RGBeter/Neptune/32X_main1.kicad_sch

## KiCad design 32X_main1.kicad_sch (2025-06-25, an earlier design)

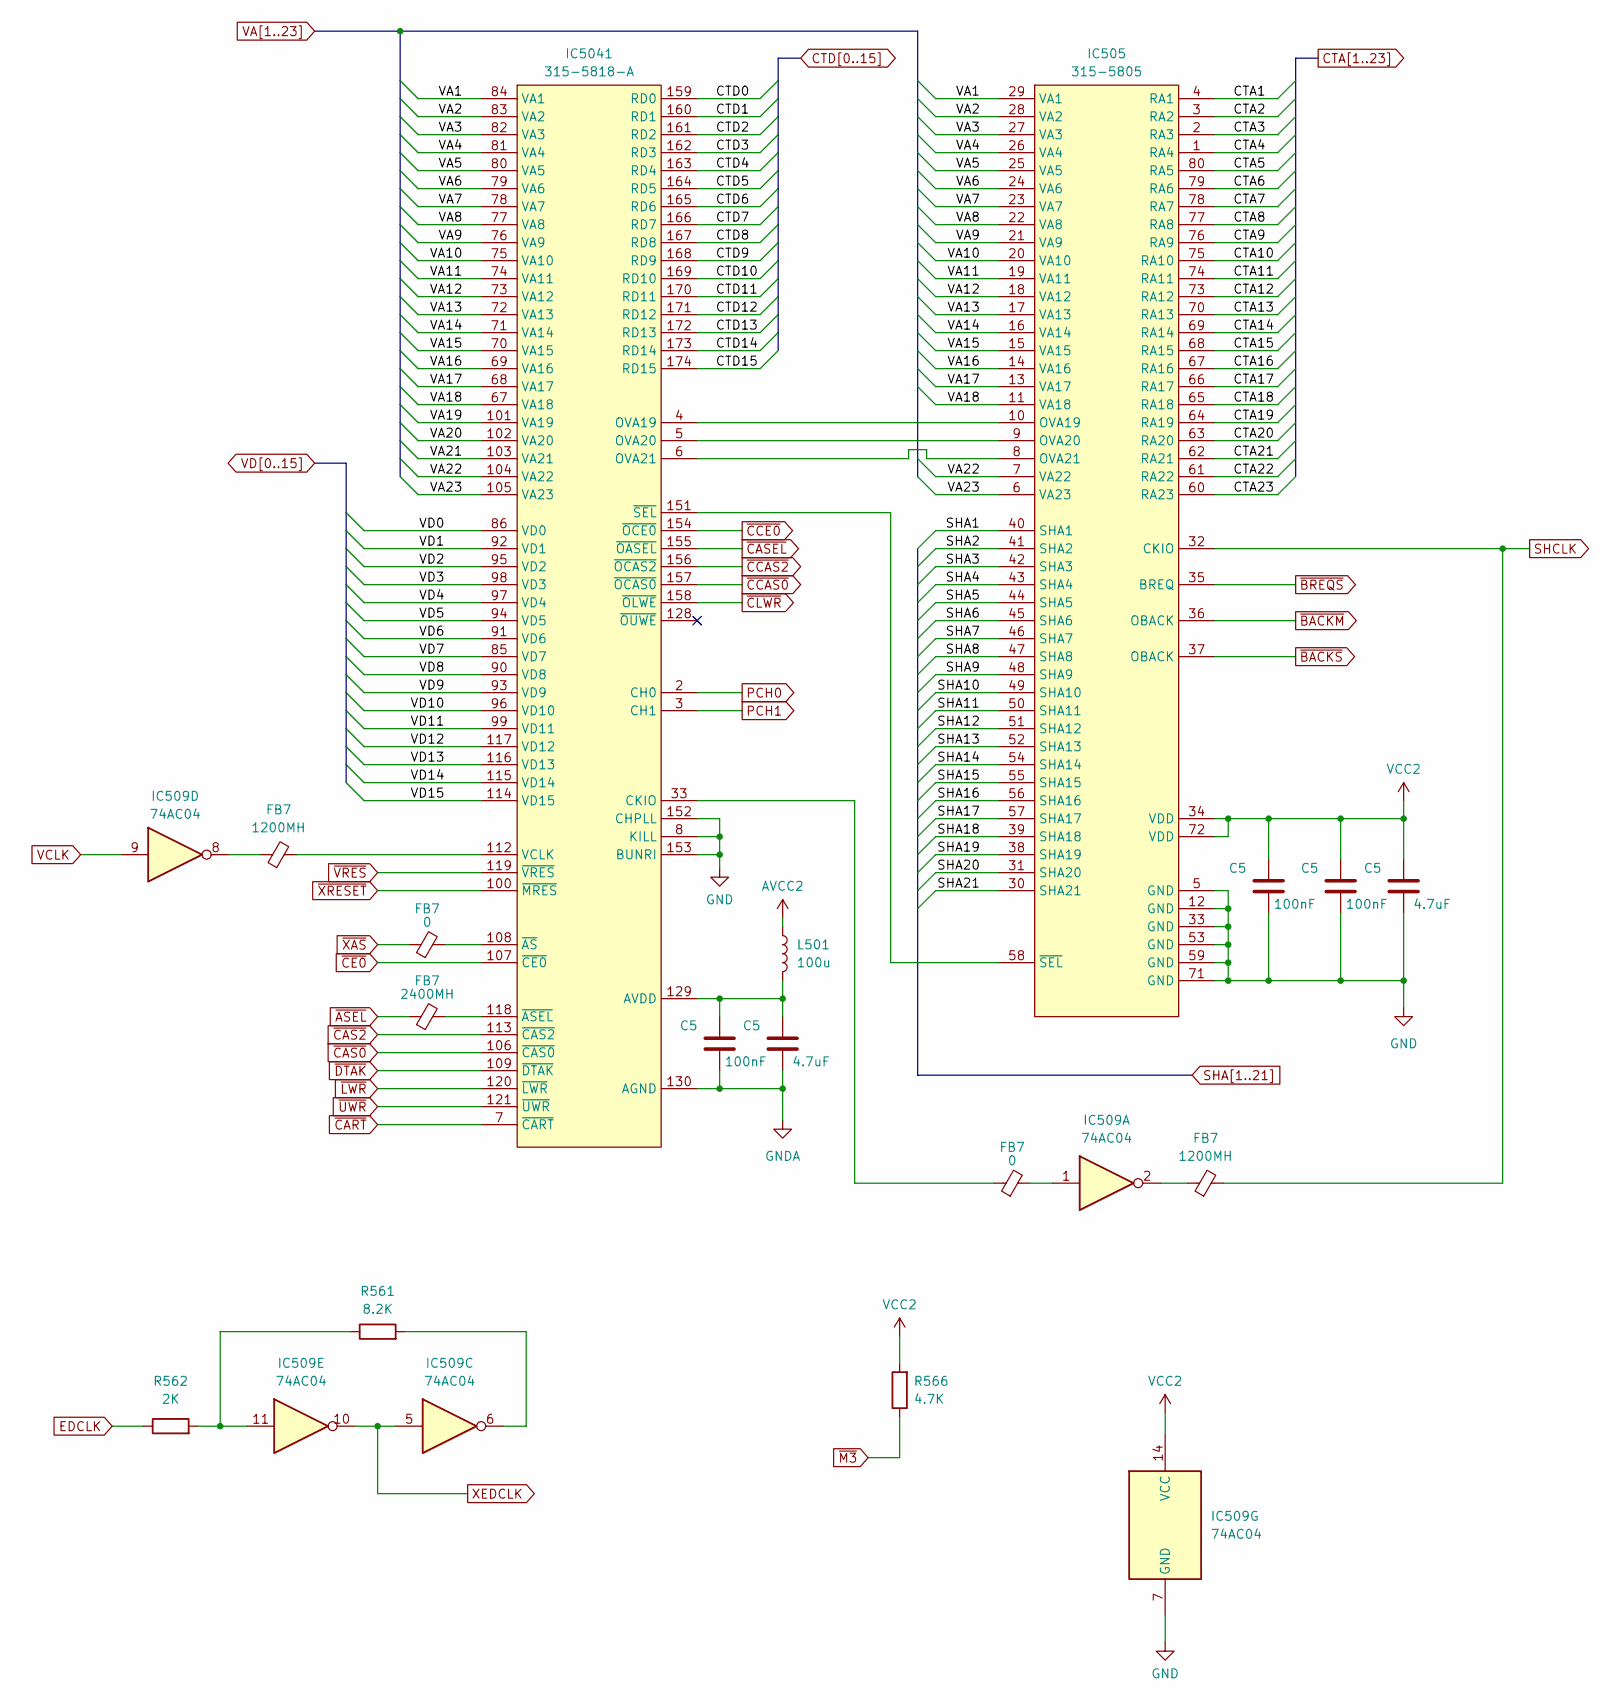
[picture p8: schematic 32X_main1.kicad_sch]

Parts:
C5: 100nF
FB7: 1200MH
IC505: 315-5805
IC509: 74AC04
IC5041: 315-5818-A
L501: 100u
R561: 8.2K
R562: 2K
R566: 4.7K

Connections:
AVCC2: L501.1
CTA1: IC505.4 (RA1)
CTA2: IC505.3 (RA2)
CTA3: IC505.2 (RA3)
CTA4: IC505.1 (RA4)
CTA5: IC505.80 (RA5)
CTA6: IC505.79 (RA6)
CTA7: IC505.78 (RA7)
CTA8: IC505.77 (RA8)
CTA9: IC505.76 (RA9)
CTA10: IC505.75 (RA10)
CTA11: IC505.74 (RA11)
CTA12: IC505.73 (RA12)
CTA13: IC505.70 (RA13)
CTA14: IC505.69 (RA14)
CTA15: IC505.68 (RA15)
CTA16: IC505.67 (RA16)
CTA17: IC505.66 (RA17)
CTA18: IC505.65 (RA18)
CTA19: IC505.64 (RA19)
CTA20: IC505.63 (RA20)
CTA21: IC505.62 (RA21)
CTA22: IC505.61 (RA22)
CTA23: IC505.60 (RA23)
CTD0: IC5041.159 (RD0)
CTD1: IC5041.160 (RD1)
CTD2: IC5041.161 (RD2)
CTD3: IC5041.162 (RD3)
CTD4: IC5041.163 (RD4)
CTD5: IC5041.164 (RD5)
CTD6: IC5041.165 (RD6)
CTD7: IC5041.166 (RD7)
CTD8: IC5041.167 (RD8)
CTD9: IC5041.168 (RD9)
CTD10: IC5041.169 (RD10)
CTD11: IC5041.170 (RD11)
CTD12: IC5041.171 (RD12)
CTD13: IC5041.172 (RD13)
CTD14: IC5041.173 (RD14)
CTD15: IC5041.174 (RD15)
EDCLK: R562.1
GND: C5.2, IC505.5 (GND), IC505.12 (GND), IC505.33 (GND), IC505.53 (GND), IC505.59 (GND), IC505.71 (GND), IC509.7 (GND), IC5041.8 (KILL), IC5041.152 (CHPLL), IC5041.153 (BUNRI)
GNDA: C5.2, IC5041.130 (AGND)
unnamed: C5.1, IC5041.129 (AVDD), L501.2
unnamed: FB7.1, IC509.2, IC509.8, IC5041.33 (CKIO)
unnamed: FB7.2, IC509.1, IC5041.108 (~AS), IC5041.112 (VCLK), IC5041.118 (~ASEL)
unnamed: IC509.6, R561.2
unnamed: IC509.11, R561.1, R562.2
unnamed: IC505.10 (OVA19), IC5041.4 (OVA19)
unnamed: IC505.9 (OVA20), IC5041.5 (OVA20)
unnamed: IC505.8 (OVA21), IC5041.6 (OVA21)
unnamed: IC505.58 (~SEL), IC5041.151 (~SEL)
PCH0: IC5041.2 (CH0)
PCH1: IC5041.3 (CH1)
SHA1: IC505.40 (SHA1)
SHA2: IC505.41 (SHA2)
SHA3: IC505.42 (SHA3)
SHA4: IC505.43 (SHA4)
SHA5: IC505.44 (SHA5)
SHA6: IC505.45 (SHA6)
SHA7: IC505.46 (SHA7)
SHA8: IC505.47 (SHA8)
SHA9: IC505.48 (SHA9)
SHA10: IC505.49 (SHA10)
SHA11: IC505.50 (SHA11)
SHA12: IC505.51 (SHA12)
SHA13: IC505.52 (SHA13)
SHA14: IC505.54 (SHA14)
SHA15: IC505.55 (SHA15)
SHA16: IC505.56 (SHA16)
SHA17: IC505.57 (SHA17)
SHA18: IC505.39 (SHA18)
SHA19: IC505.38 (SHA19)
SHA20: IC505.31 (SHA20)
SHA21: IC505.30 (SHA21)
SHCLK: FB7.2, IC505.32 (CKIO)
VA1: IC505.29 (VA1), IC5041.84 (VA1)
VA2: IC505.28 (VA2), IC5041.83 (VA2)
VA3: IC505.27 (VA3), IC5041.82 (VA3)
VA4: IC505.26 (VA4), IC5041.81 (VA4)
VA5: IC505.25 (VA5), IC5041.80 (VA5)
VA6: IC505.24 (VA6), IC5041.79 (VA6)
VA7: IC505.23 (VA7), IC5041.78 (VA7)
VA8: IC505.22 (VA8), IC5041.77 (VA8)
VA9: IC505.21 (VA9), IC5041.76 (VA9)
VA10: IC505.20 (VA10), IC5041.75 (VA10)
VA11: IC505.19 (VA11), IC5041.74 (VA11)
VA12: IC505.18 (VA12), IC5041.73 (VA12)
VA13: IC505.17 (VA13), IC5041.72 (VA13)
VA14: IC505.16 (VA14), IC5041.71 (VA14)
VA15: IC505.15 (VA15), IC5041.70 (VA15)
VA16: IC505.14 (VA16), IC5041.69 (VA16)
VA17: IC505.13 (VA17), IC5041.68 (VA17)
VA18: IC505.11 (VA18), IC5041.67 (VA18)
VA19: IC5041.101 (VA19)
VA20: IC5041.102 (VA20)
VA21: IC5041.103 (VA21)
VA22: IC505.7 (VA22), IC5041.104 (VA22)
VA23: IC505.6 (VA23), IC5041.105 (VA23)
VCC2: C5.1, IC505.34 (VDD), IC505.72 (VDD), IC509.14 (VCC), R566.2
VCLK: IC509.9
VD0: IC5041.86 (VD0)
VD1: IC5041.92 (VD1)
VD2: IC5041.95 (VD2)
VD3: IC5041.98 (VD3)
VD4: IC5041.97 (VD4)
VD5: IC5041.94 (VD5)
VD6: IC5041.91 (VD6)
VD7: IC5041.85 (VD7)
VD8: IC5041.90 (VD8)
VD9: IC5041.93 (VD9)
VD10: IC5041.96 (VD10)
VD11: IC5041.99 (VD11)
VD12: IC5041.117 (VD12)
VD13: IC5041.116 (VD13)
VD14: IC5041.115 (VD14)
VD15: IC5041.114 (VD15)
XEDCLK: IC509.5, IC509.10
~ASEL: FB7.1
~BACKM: IC505.36 (OBACK)
~BACKS: IC505.37 (OBACK)
~BREQS: IC505.35 (BREQ)
~CART: IC5041.7 (~CART)
~CAS0: IC5041.106 (~CAS0)
~CAS2: IC5041.113 (~CAS2)
~CASEL: IC5041.155 (~OASEL)
~CCAS0: IC5041.157 (~OCAS0)
~CCAS2: IC5041.156 (~OCAS2)
~CCE0: IC5041.154 (~OCE0)
~CE0: IC5041.107 (~CE0)
~CLWR: IC5041.158 (~OLWE)
~DTAK: IC5041.109 (~DTAK)
~LWR: IC5041.120 (~LWR)
~M3: R566.1
~UWR: IC5041.121 (~UWR)
~VRES: IC5041.119 (~VRES)
~XAS: FB7.1
~XRESET: IC5041.100 (~MRES)
