RGBeter/Neptune/32X_main2.kicad_sch

## KiCad design 32X_main2.kicad_sch (2025-06-25, an earlier design)

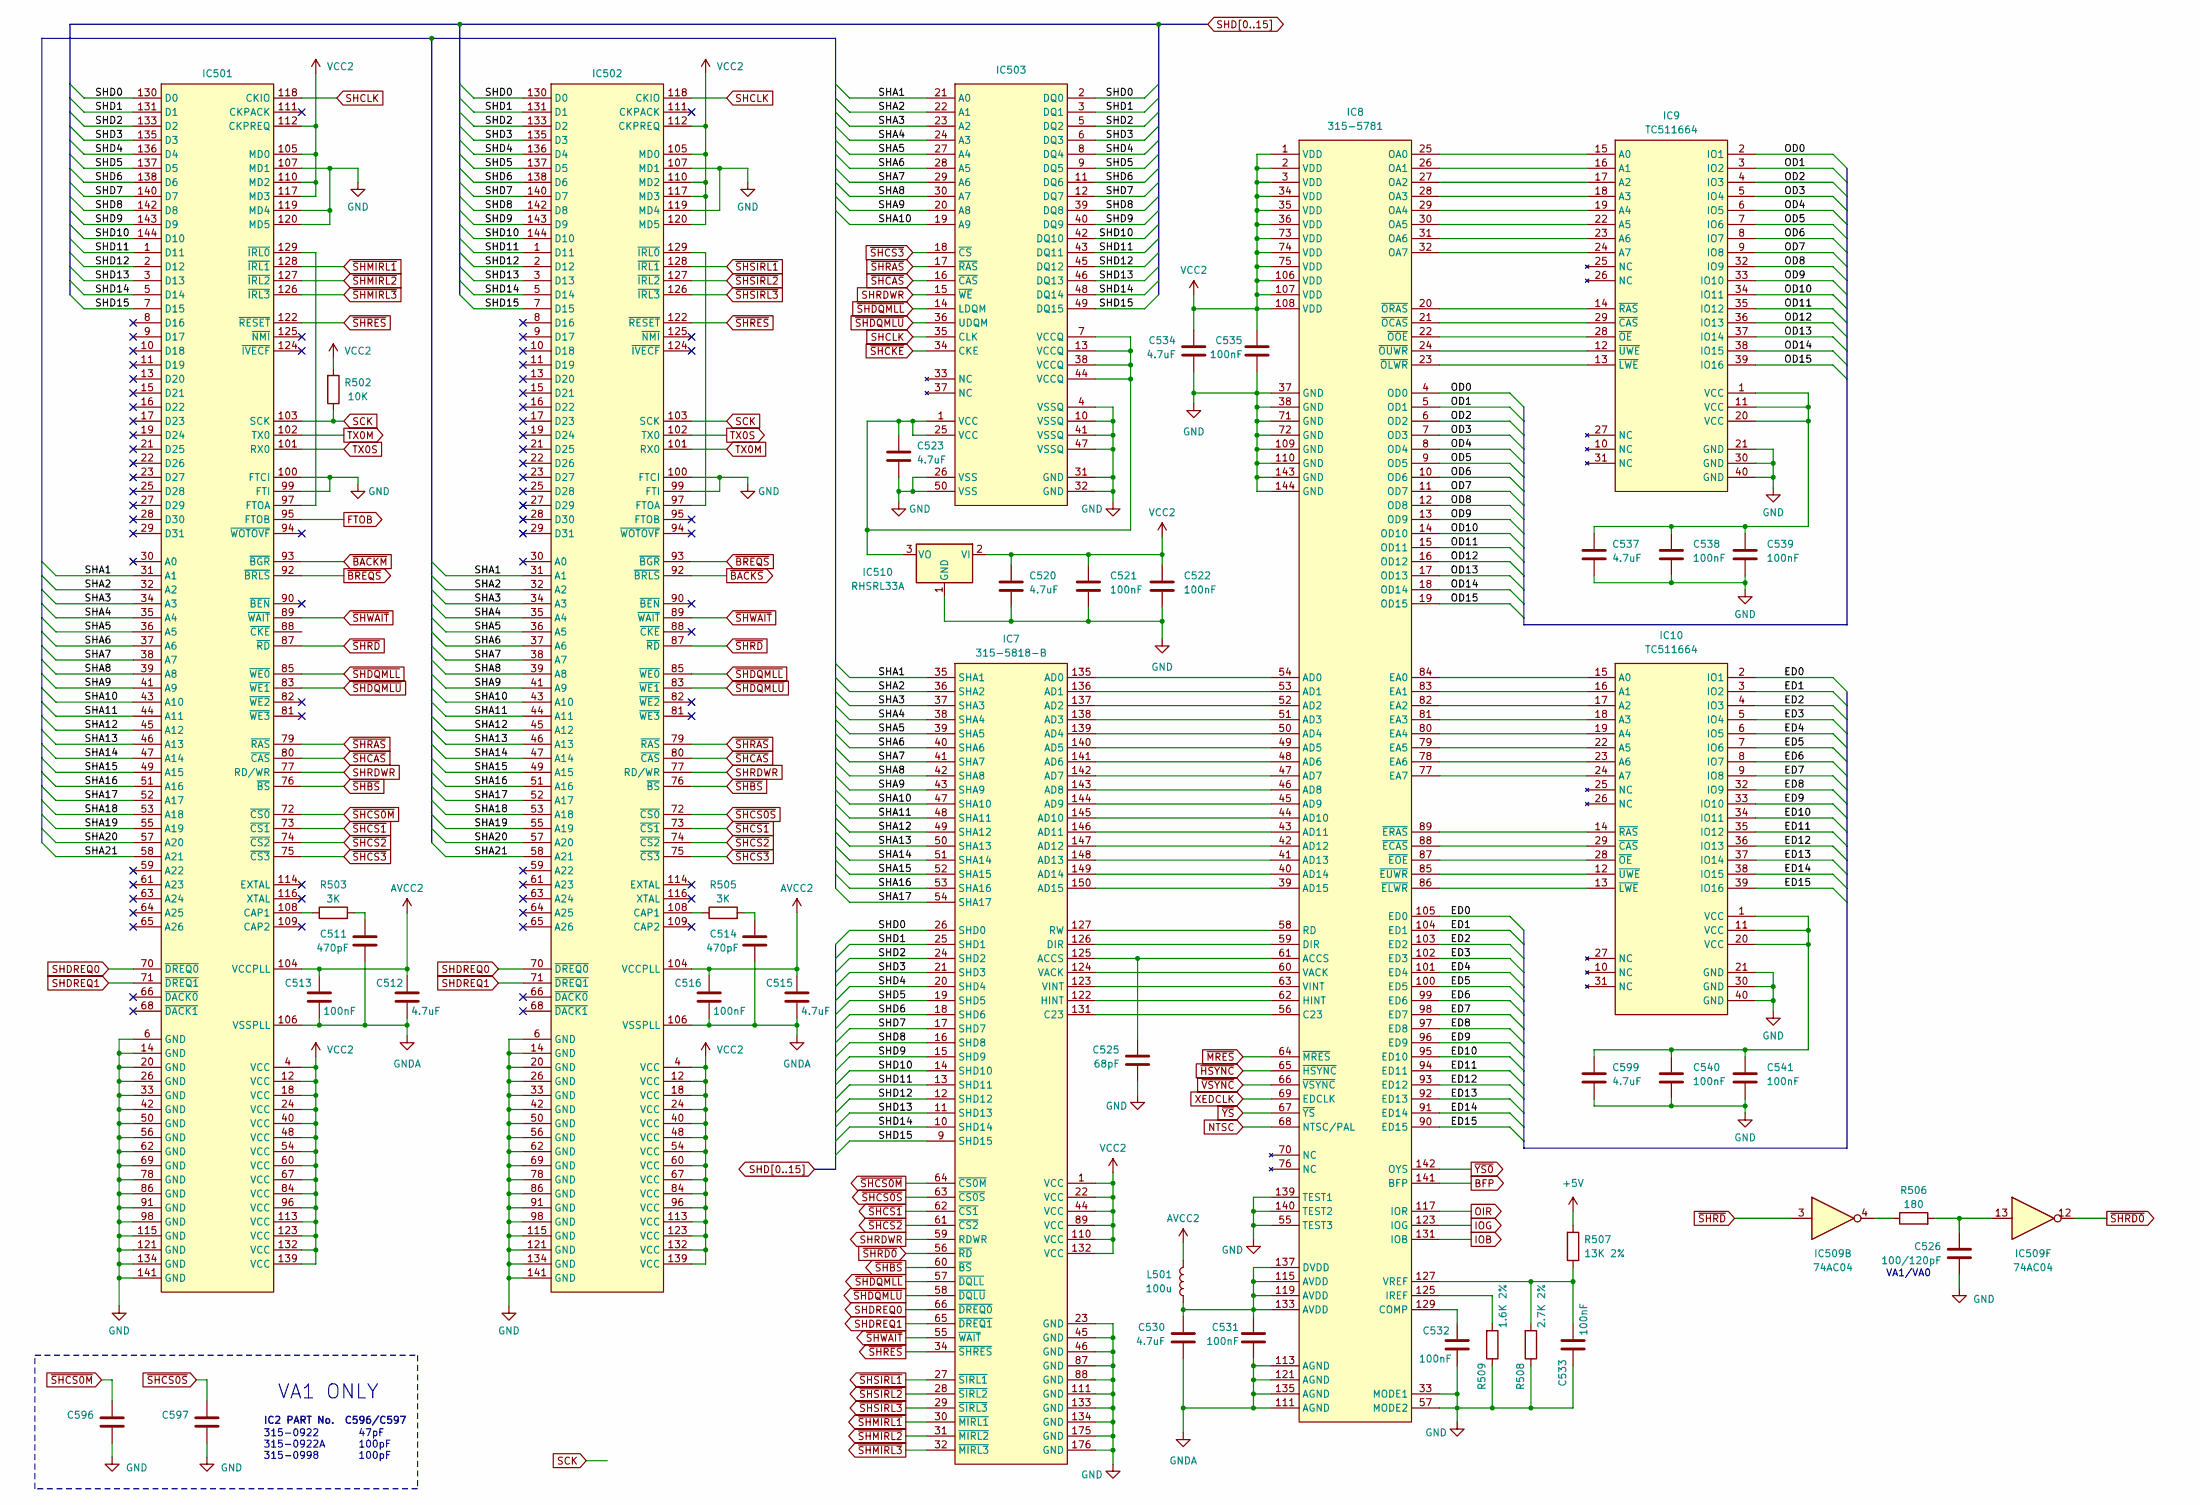
[picture p9: schematic 32X_main2.kicad_sch]

Parts:
C511, C514: 470pF
C512, C515, C520, C523, C530, C534, C537, C599: 4.7uF
C513, C516, C521, C522, C531, C532, C533, C535, C538, C539, C540, C541: 100nF
C525: 68pF
C526: 100/120pF
C596, C597: 100pF
IC7: 315-5818-B
IC8: 315-5781
IC9, IC10: TC511664
IC501, IC502, IC503: (no value)
IC509: 74AC04
IC510: RHSRL33A
L501: 100u
R502: 10K
R503, R505: 3K
R506: 180
R507: 13K 2%
R508: 2.7K 2%
R509: 1.6K 2%

Connections:
+5V: R507.2
AVCC2: C512.1, C513.1, C515.1, C516.1, IC501.104 (VCCPLL), IC502.104 (VCCPLL), L501.1
BFP: IC8.141 (BFP)
ED0: IC8.105 (ED0), IC10.2 (IO1)
ED1: IC8.104 (ED1), IC10.3 (IO2)
ED2: IC8.103 (ED2), IC10.4 (IO3)
ED3: IC8.102 (ED3), IC10.5 (IO4)
ED4: IC8.101 (ED4), IC10.6 (IO5)
ED5: IC8.100 (ED5), IC10.7 (IO6)
ED6: IC8.99 (ED6), IC10.8 (IO7)
ED7: IC8.98 (ED7), IC10.9 (IO8)
ED8: IC8.97 (ED8), IC10.32 (IO9)
ED9: IC8.96 (ED9), IC10.33 (IO10)
ED10: IC8.95 (ED10), IC10.34 (IO11)
ED11: IC8.94 (ED11), IC10.35 (IO12)
ED12: IC8.93 (ED12), IC10.36 (IO13)
ED13: IC8.92 (ED13), IC10.37 (IO14)
ED14: IC8.91 (ED14), IC10.38 (IO15)
ED15: IC8.90 (ED15), IC10.39 (IO16)
FTOB: IC501.95 (FTOB)
GND: C520.2, C521.2, C522.2, C523.2, C525.2, C526.2, C532.2, C533.2, C534.2, C535.2, C537.2, C538.2, C539.2, C540.2, C541.2, C596.2, C597.2, C599.2, IC7.23 (GND), IC7.45 (GND), IC7.46 (GND), IC7.87 (GND), IC7.88 (GND), IC7.111 (GND), IC7.133 (GND), IC7.134 (GND), IC7.175 (GND), IC7.176 (GND), IC8.33 (MODE1), IC8.37 (GND), IC8.38 (GND), IC8.55 (TEST3), IC8.57 (MODE2), IC8.71 (GND), IC8.72 (GND), IC8.109 (GND), IC8.110 (GND), IC8.139 (TEST1), IC8.140 (TEST2), IC8.143 (GND), IC8.144 (GND), IC9.21 (GND), IC9.30 (GND), IC9.40 (GND), IC10.21 (GND), IC10.30 (GND), IC10.40 (GND), IC501.6 (GND), IC501.14 (GND), IC501.20 (GND), IC501.26 (GND), IC501.33 (GND), IC501.42 (GND), IC501.50 (GND), IC501.56 (GND), IC501.62 (GND), IC501.69 (GND), IC501.78 (GND), IC501.86 (GND), IC501.91 (GND), IC501.98 (GND), IC501.99 (FTI), IC501.100 (FTCI), IC501.107 (MD1), IC501.115 (GND), IC501.119 (MD4), IC501.120 (MD5), IC501.121 (GND), IC501.134 (GND), IC501.141 (GND), IC502.6 (GND), IC502.14 (GND), IC502.20 (GND), IC502.26 (GND), IC502.33 (GND), IC502.42 (GND), IC502.50 (GND), IC502.56 (GND), IC502.62 (GND), IC502.69 (GND), IC502.78 (GND), IC502.86 (GND), IC502.91 (GND), IC502.98 (GND), IC502.99 (FTI), IC502.100 (FTCI), IC502.107 (MD1), IC502.115 (GND), IC502.119 (MD4), IC502.121 (GND), IC502.134 (GND), IC502.141 (GND), IC503.4 (VSSQ), IC503.10 (VSSQ), IC503.26 (VSS), IC503.31 (GND), IC503.32 (GND), IC503.41 (VSSQ), IC503.47 (VSSQ), IC503.50 (VSS), IC510.1 (GND), R508.1, R509.1
GNDA: C511.2, C512.2, C513.2, C514.2, C515.2, C516.2, C530.2, C531.2, IC8.111 (AGND), IC8.113 (AGND), IC8.121 (AGND), IC8.135 (AGND), IC501.106 (VSSPLL), IC502.106 (VSSPLL)
IOB: IC8.131 (IOB)
IOG: IC8.123 (IOG)
NTSC: IC8.68 (NTSC/PAL)
unnamed: C511.1, R503.2
unnamed: C514.1, R505.2
unnamed: C523.1, IC503.1 (VCC), IC503.7 (VCCQ), IC503.13 (VCCQ), IC503.25 (VCC), IC503.38 (VCCQ), IC503.44 (VCCQ), IC510.3 (VO)
unnamed: C525.1, IC7.125 (ACCS), IC8.61 (ACCS)
unnamed: C526.1, IC509.13, R506.2
unnamed: C530.1, C531.1, IC8.115 (AVDD), IC8.119 (AVDD), IC8.133 (AVDD), IC8.137 (DVDD), L501.2
unnamed: C532.1, IC8.129 (COMP)
unnamed: C533.1, IC8.127 (VREF), R507.1, R508.2
unnamed: C537.1, C538.1, C539.1, IC9.1 (VCC), IC9.11 (VCC), IC9.20 (VCC)
unnamed: C540.1, C541.1, C599.1, IC10.1 (VCC), IC10.11 (VCC), IC10.20 (VCC)
unnamed: IC7.122 (HINT), IC8.62 (HINT)
unnamed: IC7.123 (VINT), IC8.63 (VINT)
unnamed: IC7.124 (VACK), IC8.60 (VACK)
unnamed: IC7.126 (DIR), IC8.59 (DIR)
unnamed: IC7.127 (RW), IC8.58 (RD)
unnamed: IC7.131 (C23), IC8.56 (C23)
unnamed: IC7.135 (AD0), IC8.54 (AD0)
unnamed: IC7.136 (AD1), IC8.53 (AD1)
unnamed: IC7.137 (AD2), IC8.52 (AD2)
unnamed: IC7.138 (AD3), IC8.51 (AD3)
unnamed: IC7.139 (AD4), IC8.50 (AD4)
unnamed: IC7.140 (AD5), IC8.49 (AD5)
unnamed: IC7.141 (AD6), IC8.48 (AD6)
unnamed: IC7.142 (AD7), IC8.47 (AD7)
unnamed: IC7.143 (AD8), IC8.46 (AD8)
unnamed: IC7.144 (AD9), IC8.45 (AD9)
unnamed: IC7.145 (AD10), IC8.44 (AD10)
unnamed: IC7.146 (AD11), IC8.43 (AD11)
unnamed: IC7.147 (AD12), IC8.42 (AD12)
unnamed: IC7.148 (AD13), IC8.41 (AD13)
unnamed: IC7.149 (AD14), IC8.40 (AD14)
unnamed: IC7.150 (AD15), IC8.39 (AD15)
unnamed: IC8.20 (~ORAS), IC9.14 (~RAS)
unnamed: IC8.21 (~OCAS), IC9.29 (~CAS)
unnamed: IC8.22 (~OOE), IC9.28 (~OE)
unnamed: IC8.23 (~OLWR), IC9.13 (~LWE)
unnamed: IC8.24 (~OUWR), IC9.12 (~UWE)
unnamed: IC8.25 (OA0), IC9.15 (A0)
unnamed: IC8.26 (OA1), IC9.16 (A1)
unnamed: IC8.27 (OA2), IC9.17 (A2)
unnamed: IC8.28 (OA3), IC9.18 (A3)
unnamed: IC8.29 (OA4), IC9.19 (A4)
unnamed: IC8.30 (OA5), IC9.22 (A5)
unnamed: IC8.31 (OA6), IC9.23 (A6)
unnamed: IC8.32 (OA7), IC9.24 (A7)
unnamed: IC8.125 (IREF), R509.2
unnamed: IC8.85 (~EUWR), IC10.12 (~UWE)
unnamed: IC8.86 (~ELWR), IC10.13 (~LWE)
unnamed: IC8.89 (~ERAS), IC10.14 (~RAS)
unnamed: IC8.84 (EA0), IC10.15 (A0)
unnamed: IC8.83 (EA1), IC10.16 (A1)
unnamed: IC8.82 (EA2), IC10.17 (A2)
unnamed: IC8.81 (EA3), IC10.18 (A3)
unnamed: IC8.80 (EA4), IC10.19 (A4)
unnamed: IC8.79 (EA5), IC10.22 (A5)
unnamed: IC8.78 (EA6), IC10.23 (A6)
unnamed: IC8.77 (EA7), IC10.24 (A7)
unnamed: IC8.87 (~EOE), IC10.28 (~OE)
unnamed: IC8.88 (~ECAS), IC10.29 (~CAS)
unnamed: IC501.108 (CAP1), R503.1
unnamed: IC501.97 (FTOA), IC501.129 (~IRL0)
unnamed: IC502.108 (CAP1), R505.1
unnamed: IC502.97 (FTOA), IC502.129 (~IRL0)
unnamed: IC509.4, R506.1
OD0: IC8.4 (OD0), IC9.2 (IO1)
OD1: IC8.5 (OD1), IC9.3 (IO2)
OD2: IC8.6 (OD2), IC9.4 (IO3)
OD3: IC8.7 (OD3), IC9.5 (IO4)
OD4: IC8.8 (OD4), IC9.6 (IO5)
OD5: IC8.9 (OD5), IC9.7 (IO6)
OD6: IC8.10 (OD6), IC9.8 (IO7)
OD7: IC8.11 (OD7), IC9.9 (IO8)
OD8: IC8.12 (OD8), IC9.32 (IO9)
OD9: IC8.13 (OD9), IC9.33 (IO10)
OD10: IC8.14 (OD10), IC9.34 (IO11)
OD11: IC8.15 (OD11), IC9.35 (IO12)
OD12: IC8.16 (OD12), IC9.36 (IO13)
OD13: IC8.17 (OD13), IC9.37 (IO14)
OD14: IC8.18 (OD14), IC9.38 (IO15)
OD15: IC8.19 (OD15), IC9.39 (IO16)
OIR: IC8.117 (IOR)
SCK: IC501.103 (SCK), IC502.103 (SCK), R502.1
SHA1: IC7.35 (SHA1), IC501.31 (A1), IC502.31 (A1), IC503.21 (A0)
SHA2: IC7.36 (SHA2), IC501.32 (A2), IC502.32 (A2), IC503.22 (A1)
SHA3: IC7.37 (SHA3), IC501.34 (A3), IC502.34 (A3), IC503.23 (A2)
SHA4: IC7.38 (SHA4), IC501.35 (A4), IC502.35 (A4), IC503.24 (A3)
SHA5: IC7.39 (SHA5), IC501.36 (A5), IC502.36 (A5), IC503.27 (A4)
SHA6: IC7.40 (SHA6), IC501.37 (A6), IC502.37 (A6), IC503.28 (A5)
SHA7: IC7.41 (SHA7), IC501.38 (A7), IC502.38 (A7), IC503.29 (A6)
SHA8: IC7.42 (SHA8), IC501.39 (A8), IC502.39 (A8), IC503.30 (A7)
SHA9: IC7.43 (SHA9), IC501.41 (A9), IC502.41 (A9), IC503.20 (A8)
SHA10: IC7.47 (SHA10), IC501.43 (A10), IC502.43 (A10), IC503.19 (A9)
SHA11: IC7.48 (SHA11), IC501.44 (A11), IC502.44 (A11)
SHA12: IC7.49 (SHA12), IC501.45 (A12), IC502.45 (A12)
SHA13: IC7.50 (SHA13), IC501.46 (A13), IC502.46 (A13)
SHA14: IC7.51 (SHA14), IC501.47 (A14), IC502.47 (A14)
SHA15: IC7.52 (SHA15), IC501.49 (A15), IC502.49 (A15)
SHA16: IC7.53 (SHA16), IC501.51 (A16), IC502.51 (A16)
SHA17: IC7.54 (SHA17), IC501.52 (A17), IC502.52 (A17)
SHA18: IC501.53 (A18), IC502.53 (A18)
SHA19: IC501.55 (A19), IC502.55 (A19)
SHA20: IC501.57 (A20), IC502.57 (A20)
SHA21: IC501.58 (A21), IC502.58 (A21)
SHCLK: IC501.118 (CKIO), IC502.118 (CKIO), IC503.35 (CLK)
SHD0: IC7.26 (SHD0), IC501.130 (D0), IC502.130 (D0), IC503.2 (DQ0)
SHD1: IC7.25 (SHD1), IC501.131 (D1), IC502.131 (D1), IC503.3 (DQ1)
SHD2: IC7.24 (SHD2), IC501.133 (D2), IC502.133 (D2), IC503.5 (DQ2)
SHD3: IC7.21 (SHD3), IC501.135 (D3), IC502.135 (D3), IC503.6 (DQ3)
SHD4: IC7.20 (SHD4), IC501.136 (D4), IC502.136 (D4), IC503.8 (DQ4)
SHD5: IC7.19 (SHD5), IC501.137 (D5), IC502.137 (D5), IC503.9 (DQ5)
SHD6: IC7.18 (SHD6), IC501.138 (D6), IC502.138 (D6), IC503.11 (DQ6)
SHD7: IC7.17 (SHD7), IC501.140 (D7), IC502.140 (D7), IC503.12 (DQ7)
SHD8: IC7.16 (SHD8), IC501.142 (D8), IC502.142 (D8), IC503.39 (DQ8)
SHD9: IC7.15 (SHD9), IC501.143 (D9), IC502.143 (D9), IC503.40 (DQ9)
SHD10: IC7.14 (SHD10), IC501.144 (D10), IC502.144 (D10), IC503.42 (DQ10)
SHD11: IC7.13 (SHD11), IC501.1 (D11), IC502.1 (D11), IC503.43 (DQ11)
SHD12: IC7.12 (SHD12), IC501.2 (D12), IC502.2 (D12), IC503.45 (DQ12)
SHD13: IC7.11 (SHD13), IC501.3 (D13), IC502.3 (D13), IC503.46 (DQ13)
SHD14: IC7.10 (SHD14), IC501.5 (D14), IC502.5 (D14), IC503.48 (DQ14)
SHD15: IC7.9 (SHD15), IC501.7 (D15), IC502.7 (D15), IC503.49 (DQ15)
SHDREQ0: IC7.66 (~DREQ0), IC501.70 (~DREQ0), IC502.70 (~DREQ0)
SHDREQ1: IC7.65 (~DREQ1), IC501.71 (~DREQ1), IC502.71 (~DREQ1)
SHRDWR: IC7.59 (RDWR), IC501.77 (RD/WR), IC502.77 (RD/WR), IC503.15 (~WE)
TX0M: IC501.102 (TX0), IC502.101 (RX0)
TX0S: IC501.101 (RX0), IC502.102 (TX0)
VCC2: C520.1, C521.1, C522.1, C534.1, C535.1, IC7.1 (VCC), IC7.22 (VCC), IC7.44 (VCC), IC7.89 (VCC), IC7.110 (VCC), IC7.132 (VCC), IC8.1 (VDD), IC8.2 (VDD), IC8.3 (VDD), IC8.34 (VDD), IC8.35 (VDD), IC8.36 (VDD), IC8.73 (VDD), IC8.74 (VDD), IC8.75 (VDD), IC8.106 (VDD), IC8.107 (VDD), IC8.108 (VDD), IC501.4 (VCC), IC501.12 (VCC), IC501.18 (VCC), IC501.24 (VCC), IC501.40 (VCC), IC501.48 (VCC), IC501.54 (VCC), IC501.60 (VCC), IC501.67 (VCC), IC501.84 (VCC), IC501.96 (VCC), IC501.105 (MD0), IC501.110 (MD2), IC501.112 (CKPREQ), IC501.113 (VCC), IC501.117 (MD3), IC501.123 (VCC), IC501.132 (VCC), IC501.139 (VCC), IC502.4 (VCC), IC502.12 (VCC), IC502.18 (VCC), IC502.24 (VCC), IC502.40 (VCC), IC502.48 (VCC), IC502.54 (VCC), IC502.60 (VCC), IC502.67 (VCC), IC502.84 (VCC), IC502.96 (VCC), IC502.105 (MD0), IC502.110 (MD2), IC502.112 (CKPREQ), IC502.113 (VCC), IC502.117 (MD3), IC502.120 (MD5), IC502.123 (VCC), IC502.132 (VCC), IC502.139 (VCC), IC510.2 (VI), R502.2
XEDCLK: IC8.69 (EDCLK)
~BACKM: IC501.93 (~BGR)
~BACKS: IC502.92 (~BRLS)
~BREQS: IC501.92 (~BRLS), IC502.93 (~BGR)
~HSYNC: IC8.65 (~HSYNC)
~MRES: IC8.64 (~MRES)
~SHBS: IC7.60 (~BS), IC501.76 (~BS), IC502.76 (~BS)
~SHCAS: IC501.80 (~CAS), IC502.80 (~CAS), IC503.16 (~CAS)
~SHCKE: IC503.34 (CKE)
~SHCS0M: C596.1, IC7.64 (~CS0M), IC501.72 (~CS0)
~SHCS0S: C597.1, IC7.63 (~CS0S), IC502.72 (~CS0)
~SHCS1: IC7.62 (~CS1), IC501.73 (~CS1), IC502.73 (~CS1)
~SHCS2: IC7.61 (~CS2), IC501.74 (~CS2), IC502.74 (~CS2)
~SHCS3: IC501.75 (~CS3), IC502.75 (~CS3), IC503.18 (~CS)
~SHDQMLL: IC7.57 (~DQLL), IC501.85 (~WE0), IC502.85 (~WE0), IC503.14 (LDQM)
~SHDQMLU: IC7.58 (~DQLU), IC501.83 (~WE1), IC502.83 (~WE1), IC503.36 (UDQM)
~SHMIRL1: IC7.30 (~MIRL1), IC501.128 (~IRL1)
~SHMIRL2: IC7.31 (~MIRL2), IC501.127 (~IRL2)
~SHMIRL3: IC7.32 (~MIRL3), IC501.126 (~IRL3)
~SHRAS: IC501.79 (~RAS), IC502.79 (~RAS), IC503.17 (~RAS)
~SHRD0: IC7.56 (~RD), IC509.12
~SHRD: IC501.87 (~RD), IC502.87 (~RD), IC509.3
~SHRES: IC7.34 (~SHRES), IC501.122 (~RESET), IC502.122 (~RESET)
~SHSIRL1: IC7.27 (~SIRL1), IC502.128 (~IRL1)
~SHSIRL2: IC7.28 (~SIRL2), IC502.127 (~IRL2)
~SHSIRL3: IC7.29 (~SIRL3), IC502.126 (~IRL3)
~SHWAIT: IC7.55 (~WAIT), IC501.89 (~WAIT), IC502.89 (~WAIT)
~VSYNC: IC8.66 (~VSYNC)
~YS0: IC8.142 (OYS)
~YS: IC8.67 (~YS)

Notes on the sheet:
315-0922 315-0922A 315-0998
VA1 ONLY
IC2 PART No.
C596/C597
47pF 100pF 100pF
VA1/VA0
