RGBeter/Neptune/32X_sub.kicad_sch

## KiCad design 32X_sub.kicad_sch (2025-06-25, an earlier design)

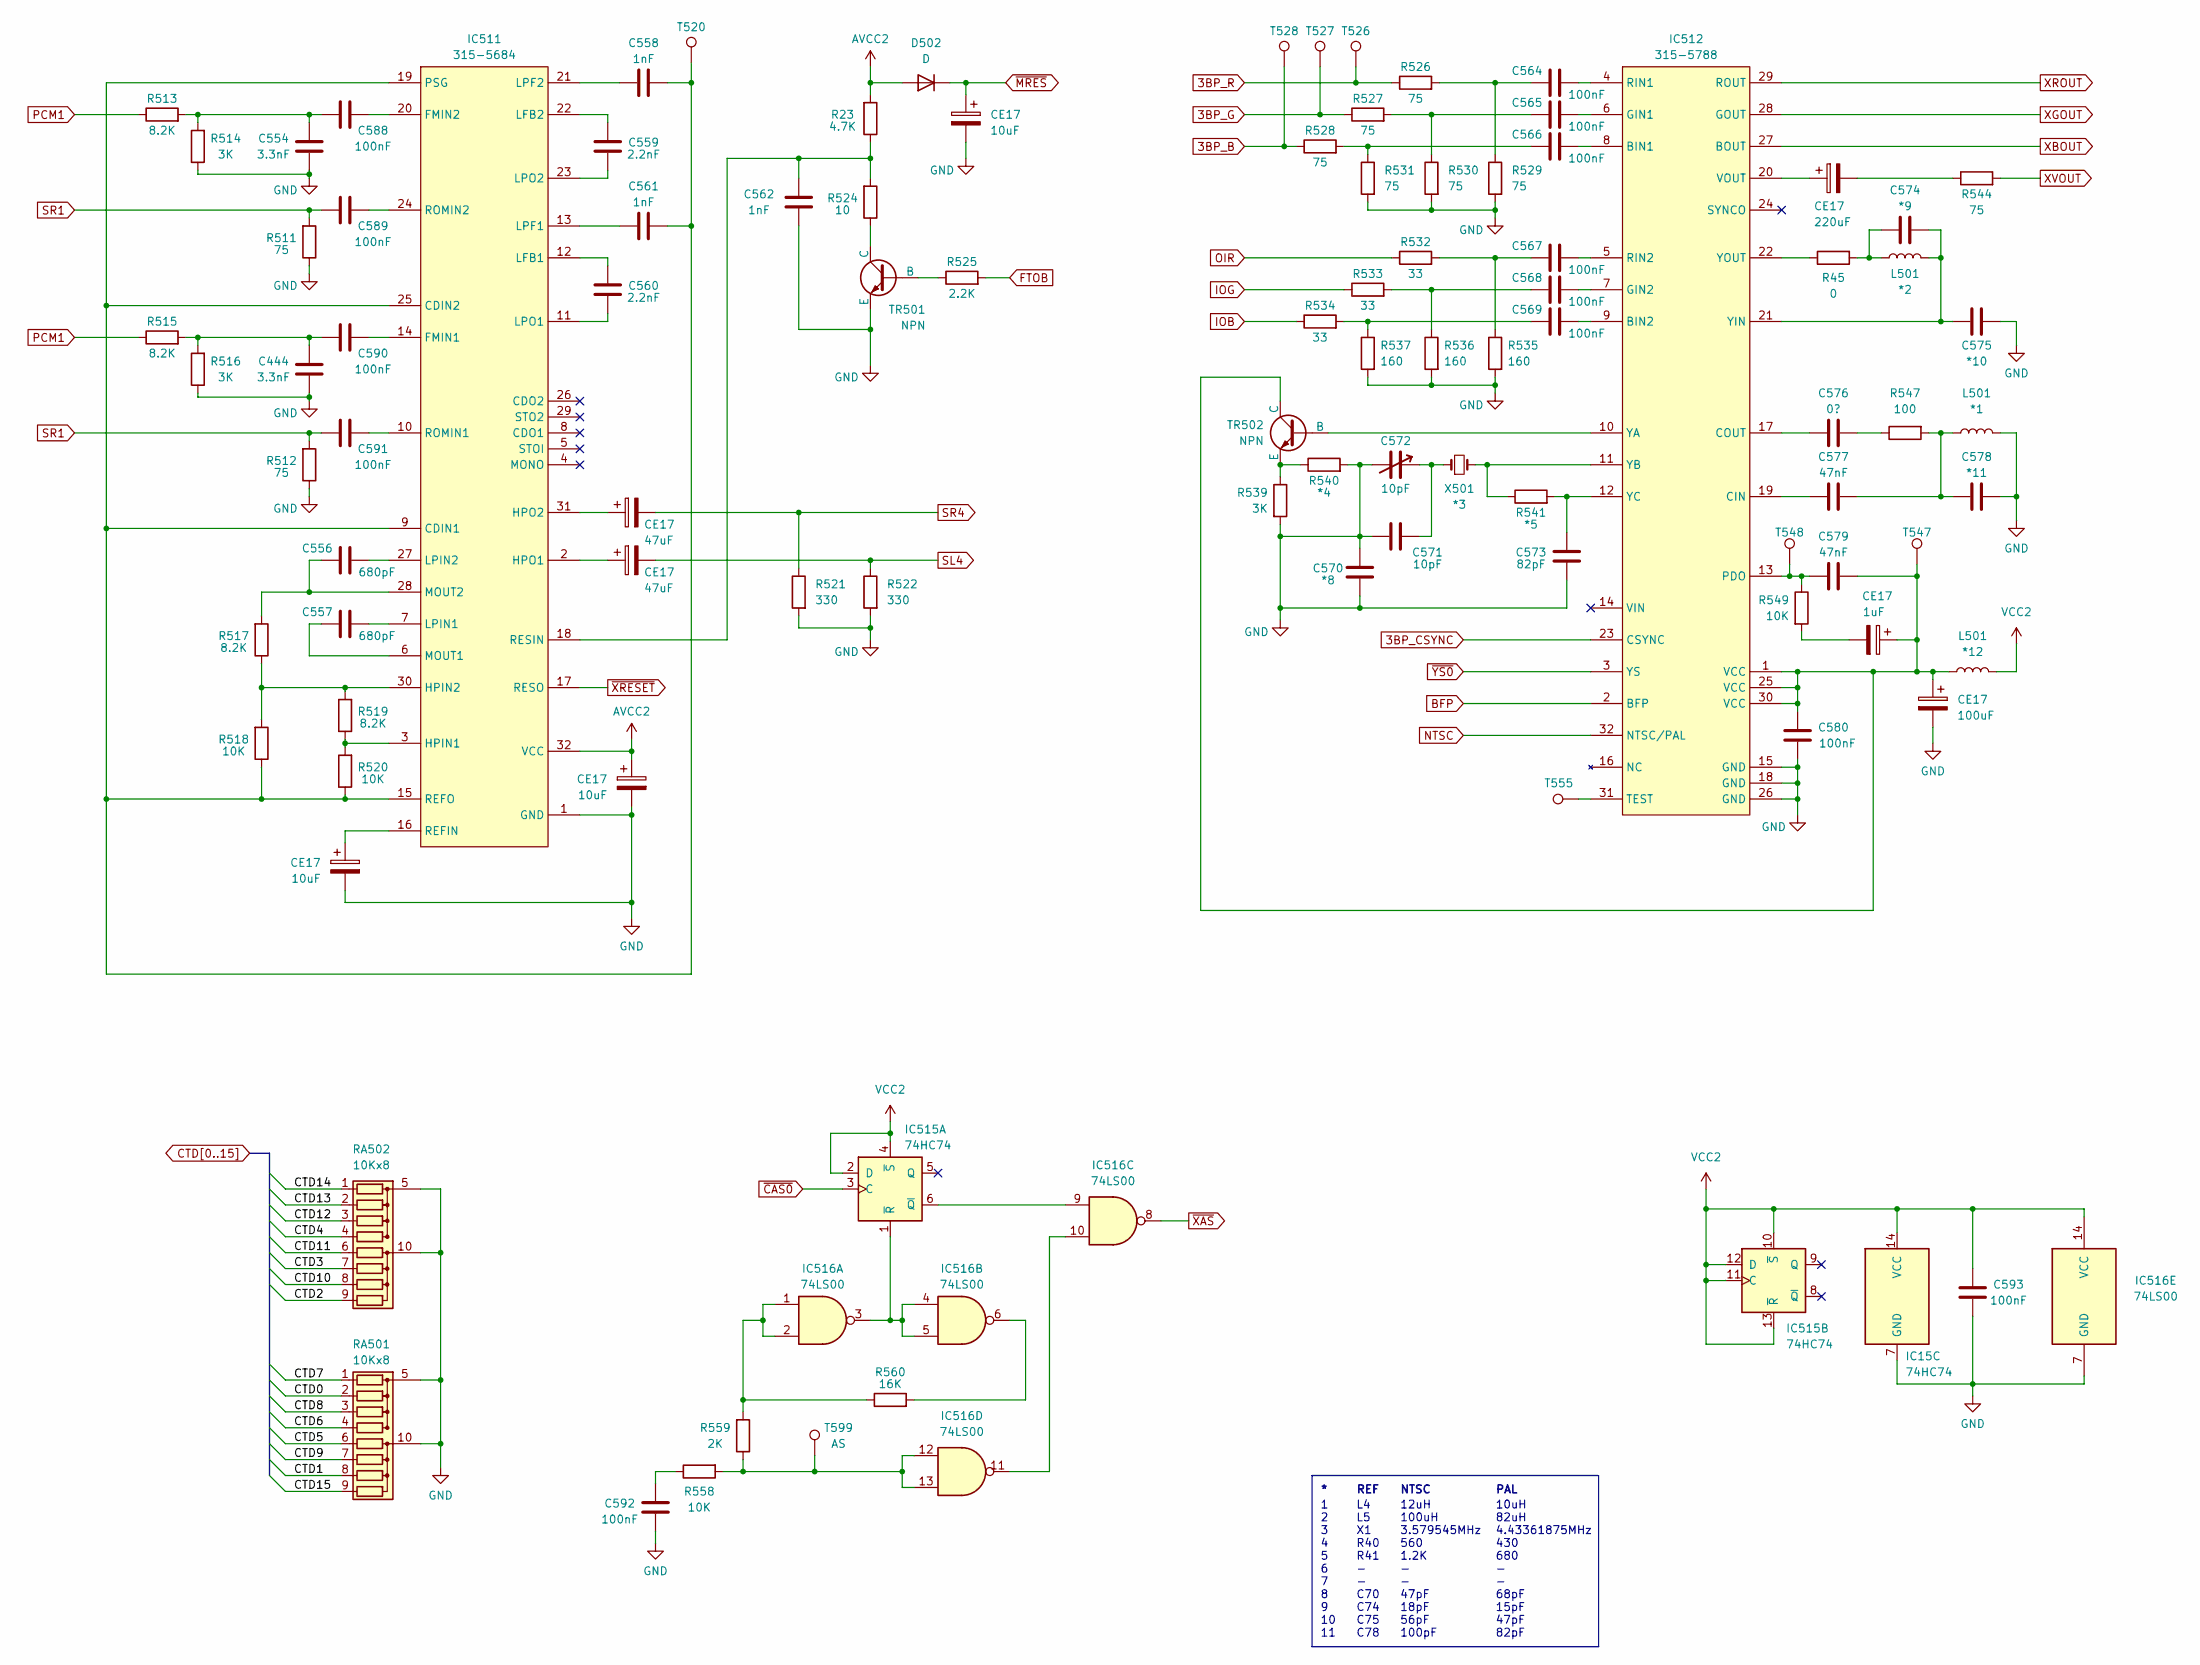
[picture p10: schematic 32X_sub.kicad_sch]

Parts:
C444, C554: 3.3nF
C556, C557: 680pF
C558, C561, C562: 1nF
C559, C560: 2.2nF
C564, C565, C566, C567, C568, C569, C580, C588, C589, C590, C591, C592, C593: 100nF
C570: *8
C571, C572: 10pF
C573: 82pF
C574: *9
C575: *10
C576: 0?
C577, C579: 47nF
C578: *11
CE17: 10uF
D502: D
IC15, IC515: 74HC74
IC511: 315-5684
IC512: 315-5788
IC516: 74LS00
L501: *2
R23: 4.7K
R45: 0
R511, R512, R526, R527, R528, R529, R530, R531, R544: 75
R513, R515, R517, R519: 8.2K
R514, R516, R539: 3K
R518, R520, R549, R558: 10K
R521, R522: 330
R524: 10
R525: 2.2K
R532, R533, R534: 33
R535, R536, R537: 160
R540: *4
R541: *5
R547: 100
R559: 2K
R560: 16K
RA501, RA502: 10Kx8
T520, T526, T527, T528, T547, T548, T555: TestPoint
T599: AS
TR501, TR502: NPN
X501: *3

Connections:
3BP_B: R528.1, T528.1
3BP_CSYNC: IC512.23 (CSYNC)
3BP_G: R527.1, T527.1
3BP_R: R526.1, T526.1
AVCC2: CE17.1, D502.2 (A), IC511.32 (VCC), R23.2
BFP: IC512.2 (BFP)
CTD0: RA501.2 (R2)
CTD1: RA501.8 (R7)
CTD2: RA502.9 (R8)
CTD3: RA502.7 (R6)
CTD4: RA502.4 (R4)
CTD5: RA501.6 (R5)
CTD6: RA501.4 (R4)
CTD7: RA501.1 (R1)
CTD8: RA501.3 (R3)
CTD9: RA501.7 (R6)
CTD10: RA502.8 (R7)
CTD11: RA502.6 (R5)
CTD12: RA502.3 (R3)
CTD13: RA502.2 (R2)
CTD14: RA502.1 (R1)
CTD15: RA501.9 (R8)
FTOB: R525.2
GND: C444.2, C554.2, C562.1, C570.1, C570.2, C571.1, C572.2, C573.1, C575.2, C578.2, C580.1, C592.1, C593.2, CE17.2, IC15.7 (GND), IC511.1 (GND), IC512.15 (GND), IC512.18 (GND), IC512.26 (GND), IC516.7 (GND), L501.2, R511.1, R512.1, R514.1, R516.1, R521.2, R522.2, R529.2, R530.2, R531.2, R535.2, R536.2, R537.2, R539.2, R540.2, RA501.5 (common), RA501.10 (common), RA502.5 (common), RA502.10 (common), TR501.3 (E)
IOB: R534.1
IOG: R533.1
NTSC: IC512.32 (NTSC/PAL)
unnamed: C444.1, C590.1, R515.2, R516.2
unnamed: C554.1, C588.1, R513.2, R514.2
unnamed: C556.1, IC511.28 (MOUT2), R517.2
unnamed: C556.2, IC511.27 (LPIN2)
unnamed: C557.1, IC511.6 (MOUT1)
unnamed: C557.2, IC511.7 (LPIN1)
unnamed: C558.1, IC511.21 (LPF2)
unnamed: C558.2, C561.2, IC511.9 (CDIN1), IC511.15 (REFO), IC511.19 (PSG), IC511.25 (CDIN2), R518.1, R520.1, T520.1
unnamed: C559.1, IC511.23 (LPO2)
unnamed: C559.2, IC511.22 (LFB2)
unnamed: C560.1, IC511.11 (LPO1)
unnamed: C560.2, IC511.12 (LFB1)
unnamed: C561.1, IC511.13 (LPF1)
unnamed: C562.2, IC511.18 (RESIN), R23.1, R524.2
unnamed: C564.1, R526.2, R529.1
unnamed: C564.2, IC512.4 (RIN1)
unnamed: C565.1, R527.2, R530.1
unnamed: C565.2, IC512.6 (GIN1)
unnamed: C566.1, R528.2, R531.1
unnamed: C566.2, IC512.8 (BIN1)
unnamed: C567.1, R532.2, R535.1
unnamed: C567.2, IC512.5 (RIN2)
unnamed: C568.1, R533.2, R536.1
unnamed: C568.2, IC512.7 (GIN2)
unnamed: C569.1, R534.2, R537.1
unnamed: C569.2, IC512.9 (BIN2)
unnamed: C571.2, C572.1, X501.1
unnamed: C573.2, IC512.12 (YC), R541.2
unnamed: C574.1, L501.1, R45.2
unnamed: C574.2, C575.1, IC512.21 (YIN), L501.2
unnamed: C576.1, IC512.17 (COUT)
unnamed: C576.2, R547.1
unnamed: C577.1, IC512.19 (CIN)
unnamed: C577.2, C578.1, L501.1, R547.2
unnamed: C579.1, IC512.13 (PDO), R549.1, T548.1
unnamed: C579.2, C580.2, CE17.1, IC512.1 (VCC), IC512.25 (VCC), IC512.30 (VCC), L501.1, T547.1, TR502.1 (C)
unnamed: C588.2, IC511.20 (FMIN2)
unnamed: C589.2, IC511.24 (ROMIN2)
unnamed: C590.2, IC511.14 (FMIN1)
unnamed: C591.2, IC511.10 (ROMIN1)
unnamed: C592.2, R558.1
unnamed: CE17.1, IC511.2 (HPO1), IC511.16 (REFIN), IC511.31 (HPO2), IC512.20 (VOUT)
unnamed: CE17.2, R544.1, R549.2
unnamed: IC511.3 (HPIN1), R519.1, R520.2
unnamed: IC511.30 (HPIN2), R517.1, R518.2, R519.2
unnamed: IC512.10 (YA), TR502.2 (B)
unnamed: IC512.11 (YB), R541.1, X501.2
unnamed: IC512.22 (YOUT), R45.1
unnamed: IC512.31 (TEST), T555.1
unnamed: IC515.1 (~R), IC516.3, IC516.4, IC516.5
unnamed: IC515.6 (~Q), IC516.9
unnamed: IC516.1, IC516.2, R559.2, R560.1
unnamed: IC516.6, R560.2
unnamed: IC516.10, IC516.11
unnamed: IC516.12, IC516.13, R558.2, R559.1, T599.1
unnamed: R524.1, TR501.1 (C)
unnamed: R525.1, TR501.2 (B)
unnamed: R539.1, R540.1, TR502.3 (E)
OIR: R532.1
PCM1: R513.1, R515.1
SL4: CE17.2, R522.1
SR1: C589.1, C591.1, R511.2, R512.2
SR4: CE17.2, R521.1
VCC2: C593.1, IC15.14 (VCC), IC515.2 (D), IC515.4 (~S), IC515.10 (~S), IC515.11 (C), IC515.12 (D), IC515.13 (~R), IC516.14 (VCC), L501.2
XBOUT: IC512.27 (BOUT)
XGOUT: IC512.28 (GOUT)
XROUT: IC512.29 (ROUT)
XVOUT: R544.2
~CAS0: IC515.3 (C)
~MRES: CE17.1, D502.1 (K)
~XAS: IC516.8
~XRESET: IC511.17 (RESO)
~YS0: IC512.3 (YS)

Notes on the sheet:
PAL
L4 L5 X1 R40 R41 - - C70 C74 C75 C78
NTSC
10uH 82uH 4.43361875MHz 430 680 - - 68pF 15pF 47pF 82pF
1 2 3 4 5 6 7 8 9 10 11
12uH 100uH 3.579545MHz 560 1.2K - - 47pF 18pF 56pF 100pF
REF
