RGBeter/Neptune/cpu.kicad_sch

## KiCad design cpu.kicad_sch (2025-06-26, an earlier design)

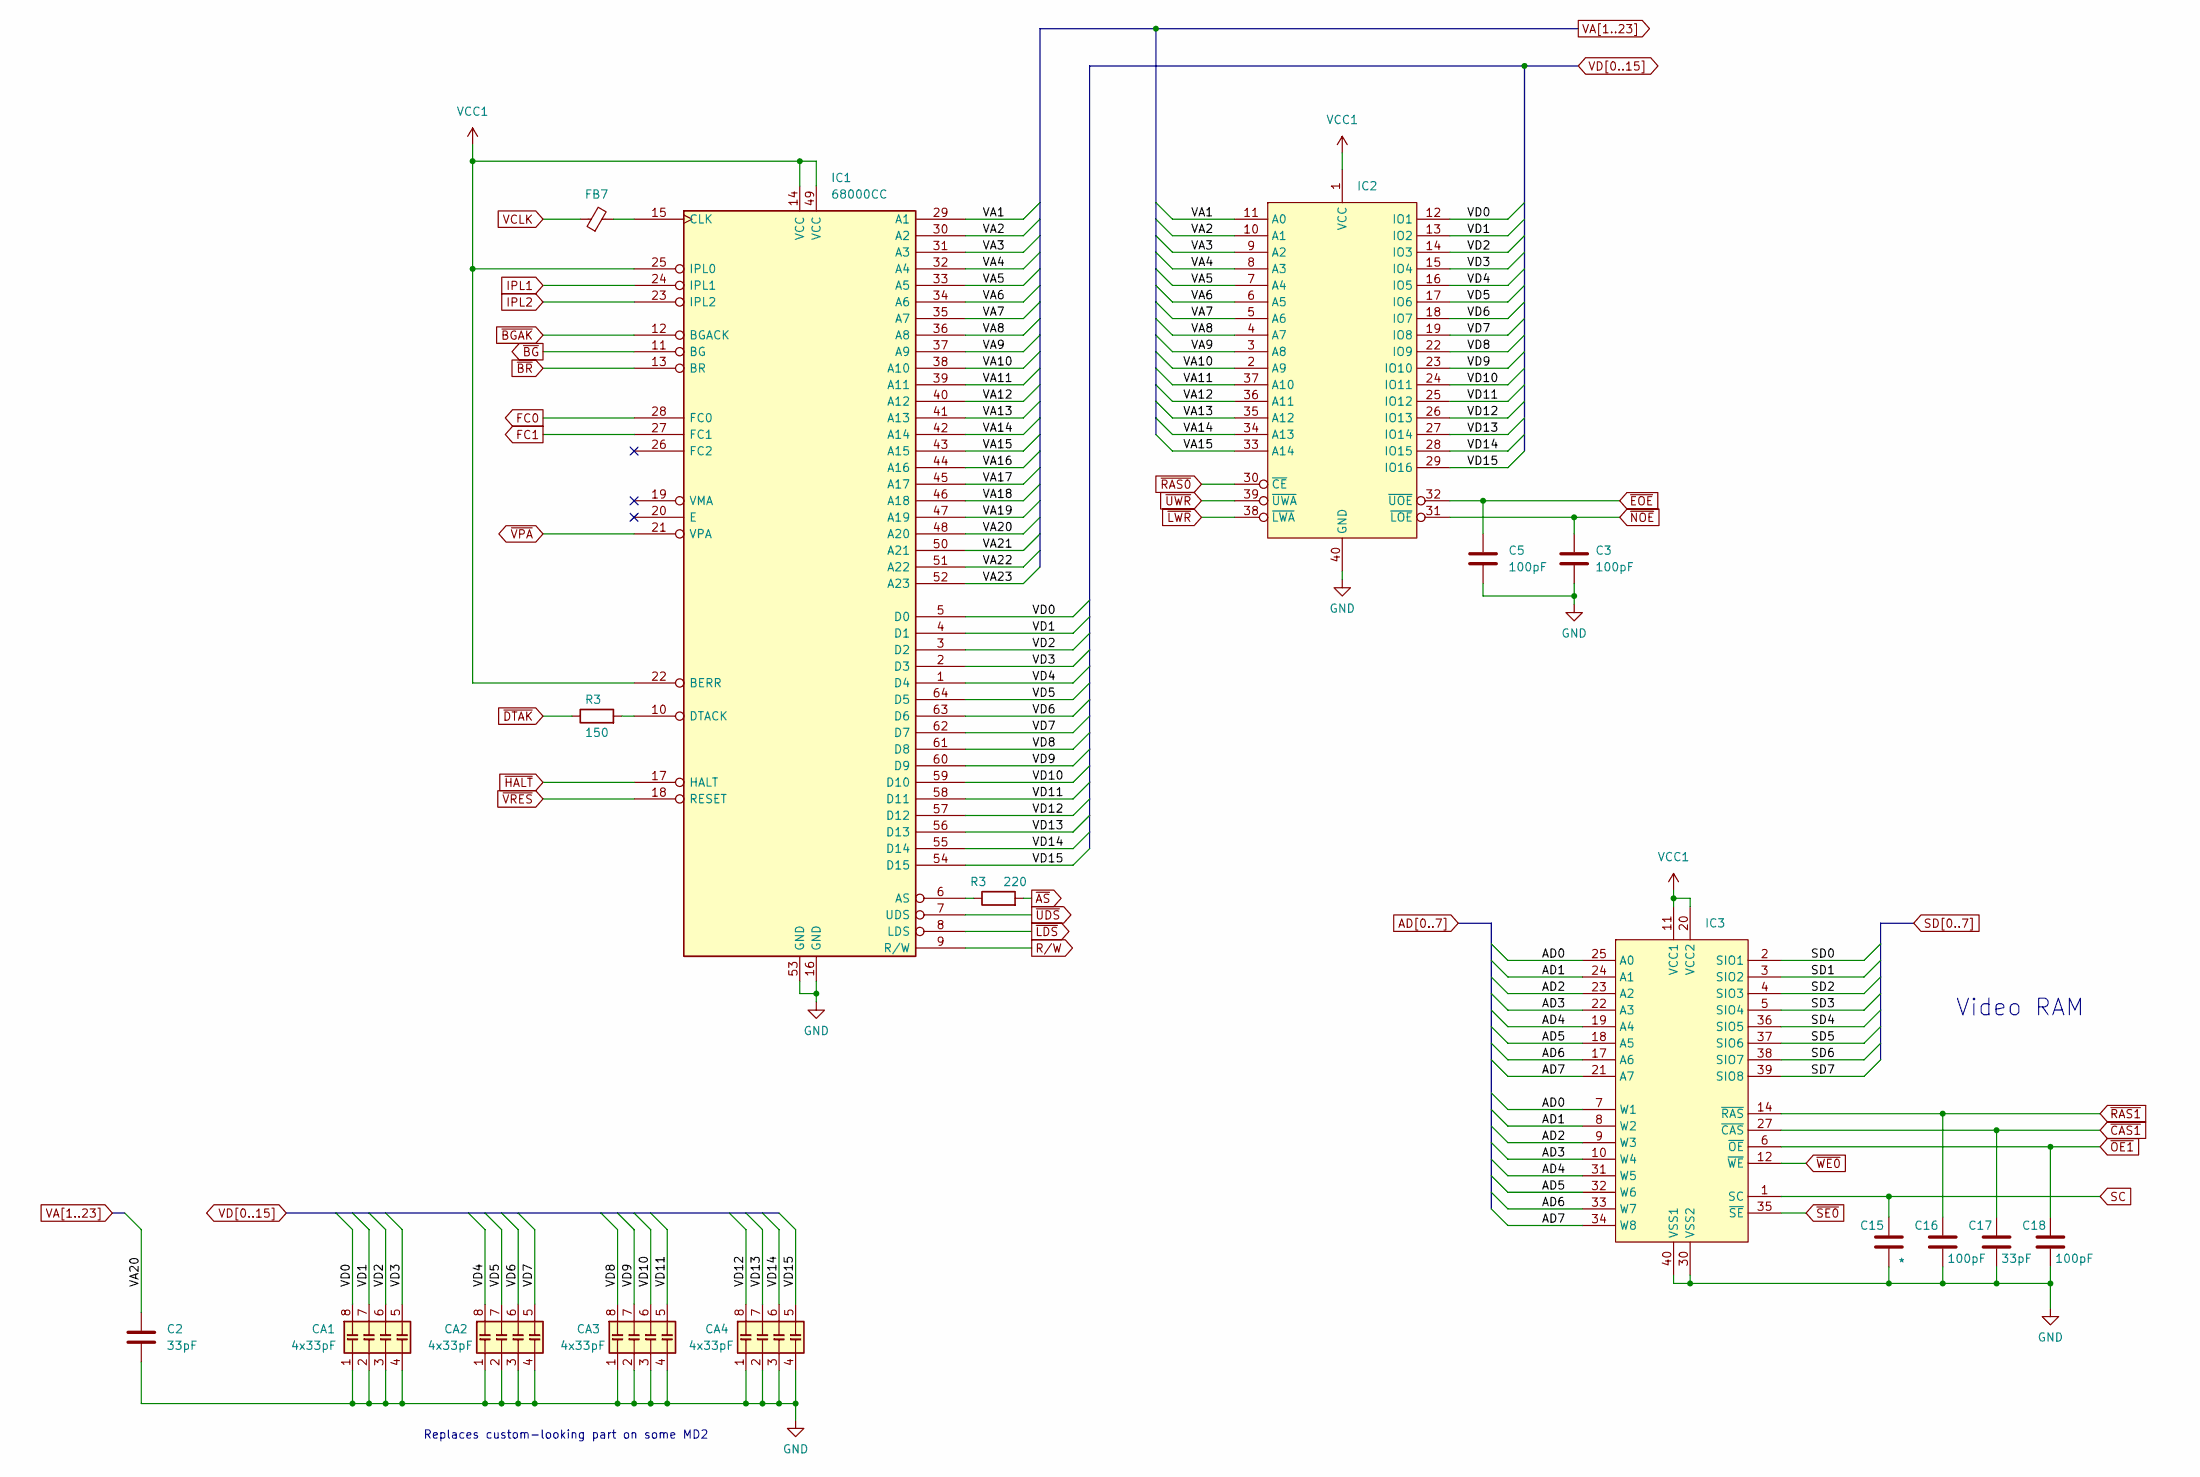
[picture p11: schematic cpu.kicad_sch]

Parts:
C2, C17: 33pF
C3, C5, C16, C18: 100pF
C15: *
CA1, CA2, CA3, CA4: 4x33pF
FB7: (no value)
IC1: 68000CC
IC2, IC3: (no value)
R3: 220

Connections:
AD0: IC3.7 (W1), IC3.25 (A0)
AD1: IC3.8 (W2), IC3.24 (A1)
AD2: IC3.9 (W3), IC3.23 (A2)
AD3: IC3.10 (W4), IC3.22 (A3)
AD4: IC3.19 (A4), IC3.31 (W5)
AD5: IC3.18 (A5), IC3.32 (W6)
AD6: IC3.17 (A6), IC3.33 (W7)
AD7: IC3.21 (A7), IC3.34 (W8)
FC0: IC1.28 (FC0)
FC1: IC1.27 (FC1)
GND: C2.2, C3.2, C5.2, C15.2, C16.2, C17.2, C18.2, CA1.1 (R1.1), CA1.2 (R2.1), CA1.3 (R3.1), CA1.4 (R4.1), CA2.1 (R1.1), CA2.2 (R2.1), CA2.3 (R3.1), CA2.4 (R4.1), CA3.1 (R1.1), CA3.2 (R2.1), CA3.3 (R3.1), CA3.4 (R4.1), CA4.1 (R1.1), CA4.2 (R2.1), CA4.3 (R3.1), CA4.4 (R4.1), IC1.16 (GND), IC1.53 (GND), IC2.40 (GND), IC3.30 (VSS2), IC3.40 (VSS1)
IPL1: IC1.24 (IPL1)
IPL2: IC1.23 (IPL2)
unnamed: FB7.2, IC1.15 (CLK)
unnamed: IC1.6 (AS), R3.1
unnamed: IC1.10 (DTACK), R3.2
R/W: IC1.9 (R/W)
SC: C15.1, IC3.1 (SC)
SD0: IC3.2 (SIO1)
SD1: IC3.3 (SIO2)
SD2: IC3.4 (SIO3)
SD3: IC3.5 (SIO4)
SD4: IC3.36 (SIO5)
SD5: IC3.37 (SIO6)
SD6: IC3.38 (SIO7)
SD7: IC3.39 (SIO8)
VA1: IC1.29 (A1), IC2.11 (A0)
VA2: IC1.30 (A2), IC2.10 (A1)
VA3: IC1.31 (A3), IC2.9 (A2)
VA4: IC1.32 (A4), IC2.8 (A3)
VA5: IC1.33 (A5), IC2.7 (A4)
VA6: IC1.34 (A6), IC2.6 (A5)
VA7: IC1.35 (A7), IC2.5 (A6)
VA8: IC1.36 (A8), IC2.4 (A7)
VA9: IC1.37 (A9), IC2.3 (A8)
VA10: IC1.38 (A10), IC2.2 (A9)
VA11: IC1.39 (A11), IC2.37 (A10)
VA12: IC1.40 (A12), IC2.36 (A11)
VA13: IC1.41 (A13), IC2.35 (A12)
VA14: IC1.42 (A14), IC2.34 (A13)
VA15: IC1.43 (A15), IC2.33 (A14)
VA16: IC1.44 (A16)
VA17: IC1.45 (A17)
VA18: IC1.46 (A18)
VA19: IC1.47 (A19)
VA20: C2.1, IC1.48 (A20)
VA21: IC1.50 (A21)
VA22: IC1.51 (A22)
VA23: IC1.52 (A23)
VCC1: IC1.14 (VCC), IC1.22 (BERR), IC1.25 (IPL0), IC1.49 (VCC), IC2.1 (VCC), IC3.11 (VCC1), IC3.20 (VCC2)
VCLK: FB7.1
VD0: CA1.8 (R1.2), IC1.5 (D0), IC2.12 (IO1)
VD1: CA1.7 (R2.2), IC1.4 (D1), IC2.13 (IO2)
VD2: CA1.6 (R3.2), IC1.3 (D2), IC2.14 (IO3)
VD3: CA1.5 (R4.2), IC1.2 (D3), IC2.15 (IO4)
VD4: CA2.8 (R1.2), IC1.1 (D4), IC2.16 (IO5)
VD5: CA2.7 (R2.2), IC1.64 (D5), IC2.17 (IO6)
VD6: CA2.6 (R3.2), IC1.63 (D6), IC2.18 (IO7)
VD7: CA2.5 (R4.2), IC1.62 (D7), IC2.19 (IO8)
VD8: CA3.8 (R1.2), IC1.61 (D8), IC2.22 (IO9)
VD9: CA3.7 (R2.2), IC1.60 (D9), IC2.23 (IO10)
VD10: CA3.6 (R3.2), IC1.59 (D10), IC2.24 (IO11)
VD11: CA3.5 (R4.2), IC1.58 (D11), IC2.25 (IO12)
VD12: CA4.8 (R1.2), IC1.57 (D12), IC2.26 (IO13)
VD13: CA4.7 (R2.2), IC1.56 (D13), IC2.27 (IO14)
VD14: CA4.6 (R3.2), IC1.55 (D14), IC2.28 (IO15)
VD15: CA4.5 (R4.2), IC1.54 (D15), IC2.29 (IO16)
~AS: R3.2
~BGAK: IC1.12 (BGACK)
~BG: IC1.11 (BG)
~BR: IC1.13 (BR)
~CAS1: C17.1, IC3.27 (~CAS)
~DTAK: R3.1
~EOE: C5.1, IC2.32 (~UOE)
~HALT: IC1.17 (HALT)
~LDS: IC1.8 (LDS)
~LWR: IC2.38 (~LWA)
~NOE: C3.1, IC2.31 (~LOE)
~OE1: C18.1, IC3.6 (~OE)
~RAS0: IC2.30 (~CE)
~RAS1: C16.1, IC3.14 (~RAS)
~SE0: IC3.35 (~SE)
~UDS: IC1.7 (UDS)
~UWR: IC2.39 (~UWA)
~VPA: IC1.21 (VPA)
~VRES: IC1.18 (RESET)
~WE0: IC3.12 (~WE)

Notes on the sheet:
Replaces custom-looking part on some MD2
Video RAM
