RGBeter/Neptune/misc.kicad_sch

## KiCad design misc.kicad_sch (2025-06-25, an earlier design)

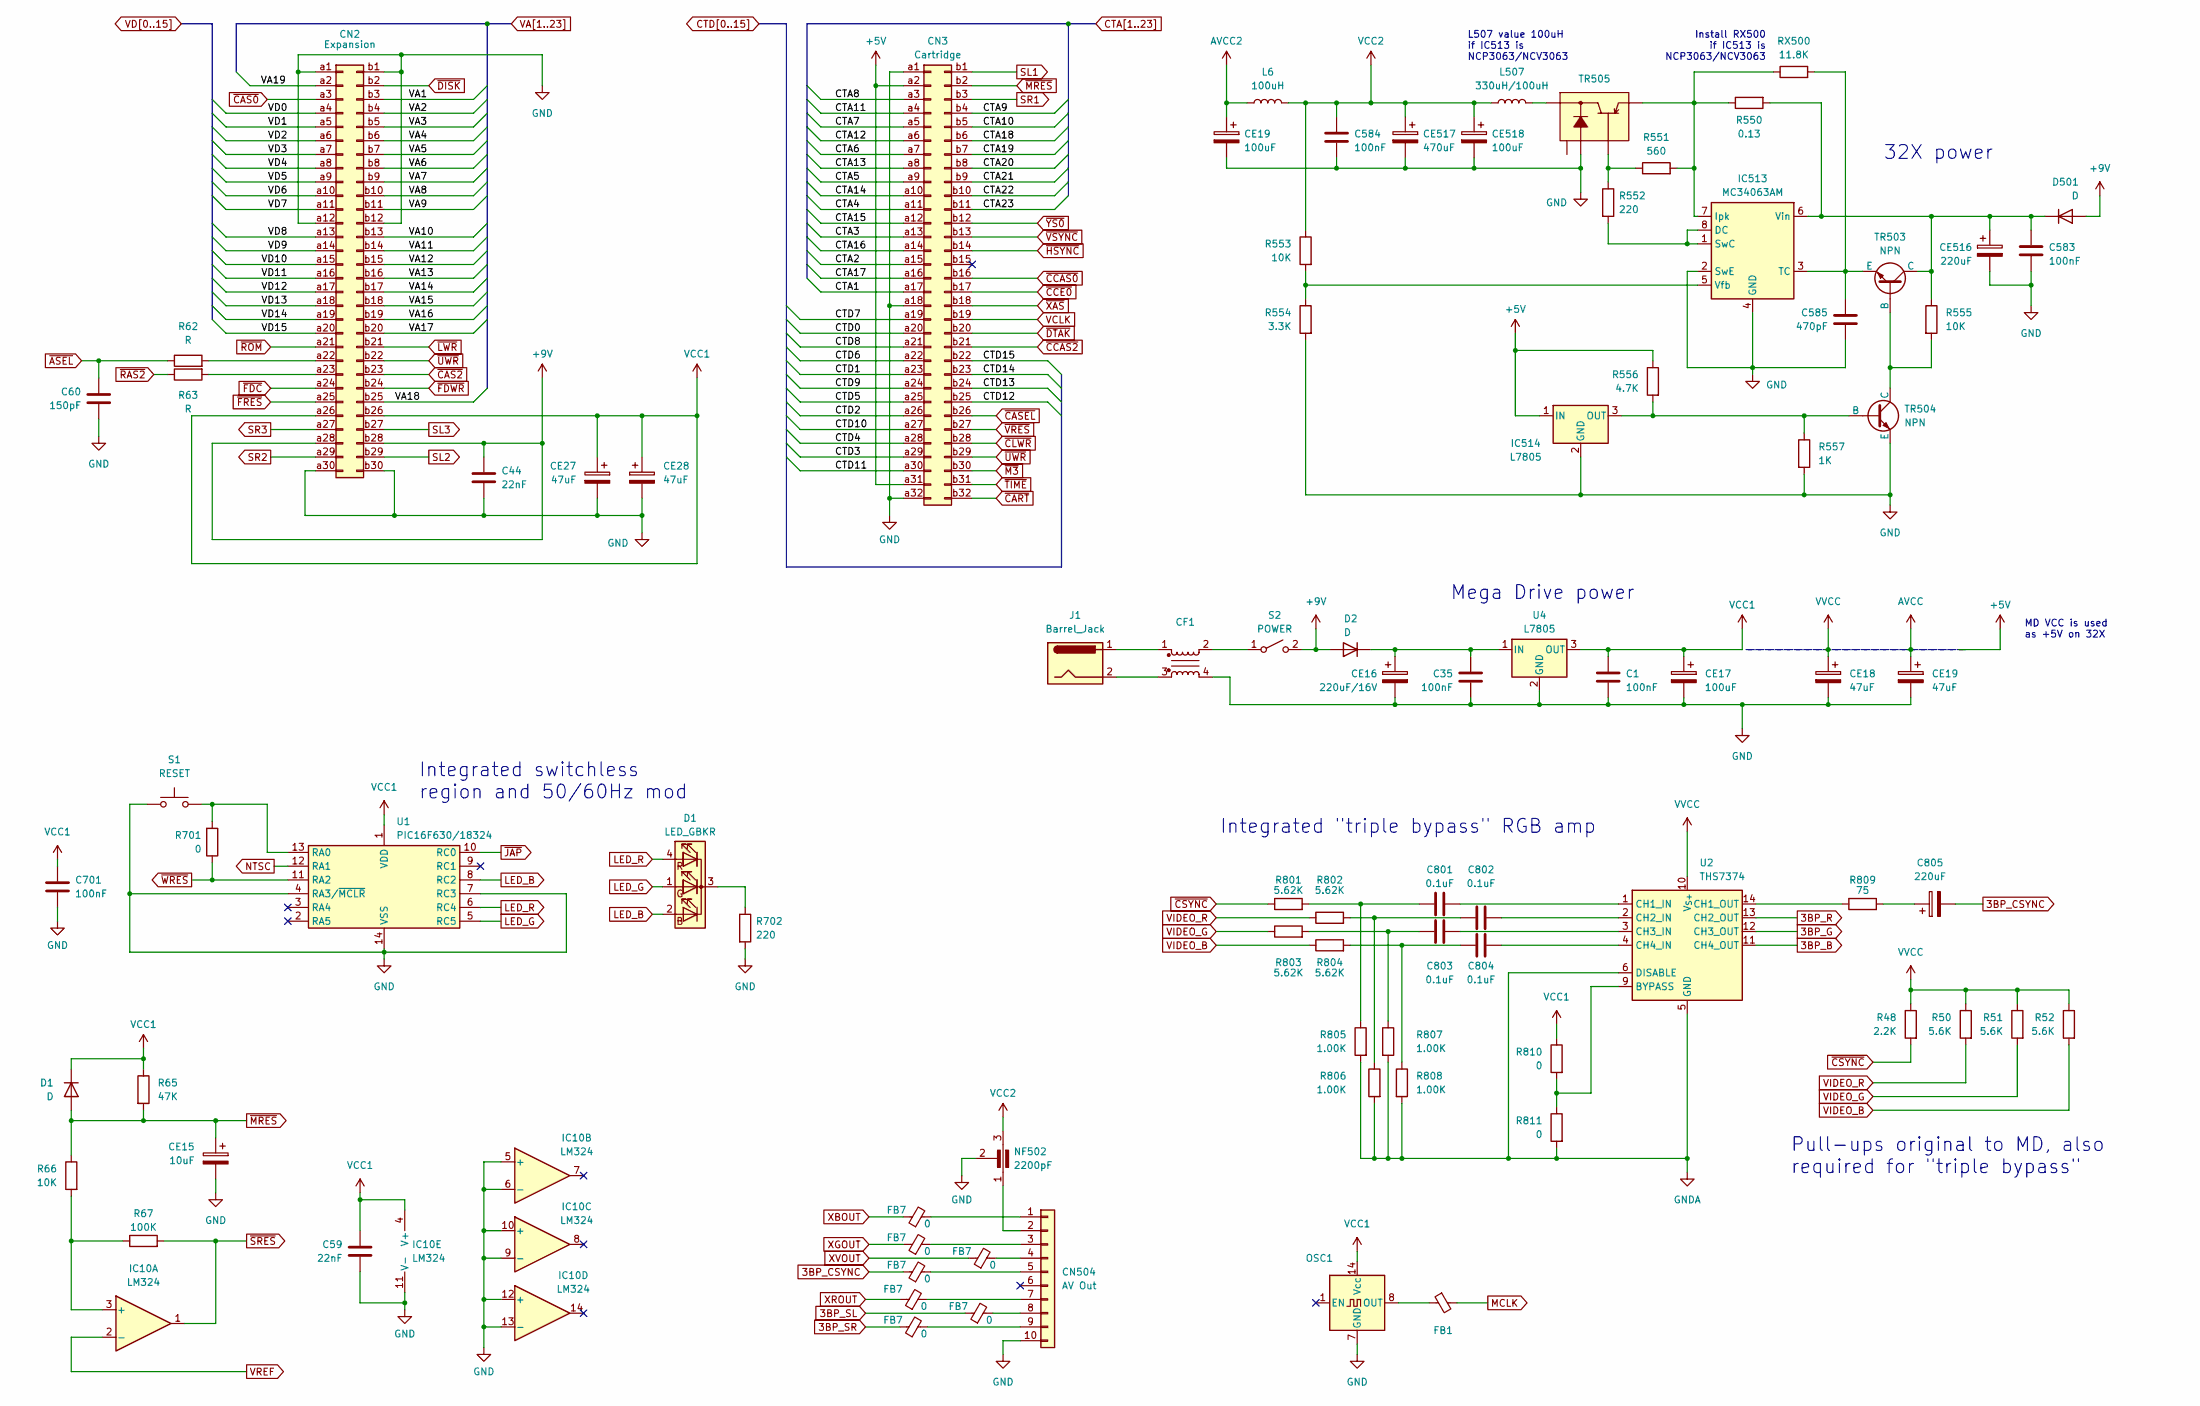
[picture p12: schematic misc.kicad_sch]

Parts:
C1, C35, C583, C584, C701: 100nF
C44, C59: 22nF
C60: 150pF
C585: 470pF
C801, C802, C803, C804: 0.1uF
C805: 220uF
CE15: 10uF
CE16: 220uF/16V
CE17, CE518: 100uF
CE18, CE19, CE27, CE28: 47uF
CE516: 220uF
CE517: 470uF
CF1: (no value)
CN2: Expansion
CN3: Cartridge
CN504: AV Out
D1, D2, D501: D
FB1: FerriteBead_Small
FB7: 0
IC10: LM324
IC513: MC34063AM; SOIC-8_3.9x4.9mm_P1.27mm
IC514: L7805
J1: Barrel_Jack
L6: 100uH
L507: 330uH/100uH
NF502: 2200pF
OSC1: CXO_DIP14; Oscillator_DIP-14
R48: 2.2K
R50, R51, R52: 5.6K
R62, R63: R
R65: 47K
R66, R553, R555: 10K
R67: 100K
R550: 0.13
R551: 560
R552, R702: 220
R554: 3.3K
R556: 4.7K
R557: 1K
R701, R810, R811: 0
R801, R802, R803, R804: 5.62K
R805, R806, R807, R808: 1.00K
R809: 75
RX500: 11.8K
S1: RESET
S2: POWER
TR503, TR504: NPN
TR505: (no value)
U1: PIC16F630/18324; SOIC-14_3.9x8.7mm_P1.27mm
U2: THS7374; TSSOP-14_4.4x5mm_P0.65mm
U4: L7805

Connections:
3BP_B: U2.11 (CH4_OUT)
3BP_CSYNC: C805.2, FB7.1
3BP_G: U2.12 (CH3_OUT)
3BP_R: U2.13 (CH2_OUT)
3BP_SL: FB7.1
3BP_SR: FB7.1
+5V: CN3.a2, CN3.a31, IC514.1 (IN), R556.1
+9V: C44.1, CN2.a28, CN2.b28, D2.2 (A), D501.2 (A), S2.2 (B)
AVCC: CE19.1
AVCC2: CE19.1, L6.1
CTA1: CN3.a17
CTA2: CN3.a15
CTA3: CN3.a13
CTA4: CN3.a11
CTA5: CN3.a9
CTA6: CN3.a7
CTA7: CN3.a5
CTA8: CN3.a3
CTA9: CN3.b4
CTA10: CN3.b5
CTA11: CN3.a4
CTA12: CN3.a6
CTA13: CN3.a8
CTA14: CN3.a10
CTA15: CN3.a12
CTA16: CN3.a14
CTA17: CN3.a16
CTA18: CN3.b6
CTA19: CN3.b7
CTA20: CN3.b8
CTA21: CN3.b9
CTA22: CN3.b10
CTA23: CN3.b11
CTD0: CN3.a20
CTD1: CN3.a23
CTD2: CN3.a26
CTD3: CN3.a29
CTD4: CN3.a28
CTD5: CN3.a25
CTD6: CN3.a22
CTD7: CN3.a19
CTD8: CN3.a21
CTD9: CN3.a24
CTD10: CN3.a27
CTD11: CN3.a30
CTD12: CN3.b25
CTD13: CN3.b24
CTD14: CN3.b23
CTD15: CN3.b22
GND: C1.2, C35.2, C44.2, C59.2, C60.2, C583.2, C584.2, C585.2, C701.2, CE15.2, CE16.2, CE17.2, CE18.2, CE19.2, CE27.2, CE28.2, CE516.2, CE517.2, CE518.2, CF1.4, CN2.a1, CN2.a12, CN2.a30, CN2.b1, CN2.b12, CN2.b30, CN3.a1, CN3.a18, CN3.a32, CN504.10, IC10.5 (+), IC10.6 (-), IC10.9 (-), IC10.10 (+), IC10.11 (V-), IC10.12 (+), IC10.13 (-), IC513.2 (SwE), IC513.4 (GND), IC514.2 (GND), NF502.2, OSC1.7 (GND), R554.2, R557.2, R702.2, S1.1, TR504.3 (E), TR505., U1.4 (RA3/~MCLR), U1.7 (RC3), U1.14 (VSS), U4.2 (GND)
GNDA: R805.2, R806.2, R807.2, R808.2, R811.2, U2.5 (GND), U2.6 (DISABLE)
LED_B: D1.2 (BA), U1.8 (RC2)
LED_G: D1.1 (GA), U1.5 (RC5)
LED_R: D1.4 (RA), U1.6 (RC4)
MCLK: FB1.2
NTSC: U1.12 (RA1)
unnamed: C35.1, CE16.1, D2.1 (K), U4.1 (IN)
unnamed: C583.1, CE516.1, D501.1 (K), IC513.6 (Vin), R550.2, R555.1, TR503.1 (C)
unnamed: C585.1, IC513.3 (TC), RX500.2, TR503.3 (E)
unnamed: C801.1, R801.2, R805.1
unnamed: C801.2, U2.1 (CH1_IN)
unnamed: C802.1, R802.2, R806.1
unnamed: C802.2, U2.2 (CH2_IN)
unnamed: C803.1, R803.2, R807.1
unnamed: C803.2, U2.3 (CH3_IN)
unnamed: C804.1, R804.2, R808.1
unnamed: C804.2, U2.4 (CH4_IN)
unnamed: C805.1, R809.2
unnamed: CF1.1, J1.1
unnamed: CF1.2, S2.1 (A)
unnamed: CF1.3, J1.2
unnamed: CN2.a22, R62.2
unnamed: CN2.a23, R63.2
unnamed: CN504.1, FB7.2
unnamed: CN504.2, NF502.1
unnamed: CN504.3, FB7.2
unnamed: CN504.4, FB7.2
unnamed: CN504.5, FB7.2
unnamed: CN504.7, FB7.2
unnamed: CN504.8, FB7.2
unnamed: CN504.9, FB7.2
unnamed: D1.3 (K), R702.1
unnamed: FB1.1, OSC1.8 (OUT)
unnamed: IC10.3 (+), R66.2, R67.1
unnamed: IC513.1 (SwC), IC513.8 (DC), R552.2
unnamed: IC513.5 (Vfb), R553.2, R554.1
unnamed: IC513.7 (Ipk), R550.1, R551.2, RX500.1, TR505.
unnamed: IC514.3 (OUT), R556.2, R557.1, TR504.2 (B)
unnamed: L507.2, TR505.
unnamed: R551.1, R552.1, TR505.
unnamed: R555.2, TR503.2 (B), TR504.1 (C)
unnamed: R701.2, S1.2, U1.13 (RA0)
unnamed: R809.1, U2.14 (CH1_OUT)
unnamed: R810.2, R811.1, U2.9 (BYPASS)
SL1: CN3.b1
SL2: CN2.b29
SL3: CN2.b27
SR1: CN3.b3
SR2: CN2.a29
SR3: CN2.a27
VA1: CN2.b3
VA2: CN2.b4
VA3: CN2.b5
VA4: CN2.b6
VA5: CN2.b7
VA6: CN2.b8
VA7: CN2.b9
VA8: CN2.b10
VA9: CN2.b11
VA10: CN2.b13
VA11: CN2.b14
VA12: CN2.b15
VA13: CN2.b16
VA14: CN2.b17
VA15: CN2.b18
VA16: CN2.b19
VA17: CN2.b20
VA18: CN2.b25
VA19: CN2.a2
VCC1: C1.1, C59.1, C701.1, CE17.1, CE27.1, CE28.1, CN2.a26, CN2.b26, D1.1 (GA), IC10.4 (V+), OSC1.14 (Vcc), R65.1, R810.1, U1.1 (VDD), U4.3 (OUT)
VCC2: C584.1, CE517.1, CE518.1, L6.2, L507.1, NF502.3, R553.1
VCLK: CN3.b19
VD0: CN2.a4
VD1: CN2.a5
VD2: CN2.a6
VD3: CN2.a7
VD4: CN2.a8
VD5: CN2.a9
VD6: CN2.a10
VD7: CN2.a11
VD8: CN2.a13
VD9: CN2.a14
VD10: CN2.a15
VD11: CN2.a16
VD12: CN2.a17
VD13: CN2.a18
VD14: CN2.a19
VD15: CN2.a20
VIDEO_B: R52.2, R804.1
VIDEO_G: R51.2, R803.1
VIDEO_R: R50.2, R802.1
VREF: IC10.2 (-)
VVCC: CE18.1, R48.1, R50.1, R51.1, R52.1, U2.10 (V_{S+})
XBOUT: FB7.1
XGOUT: FB7.1
XROUT: FB7.1
XVOUT: FB7.1
~ASEL: C60.1, R62.1
~CART: CN3.b32
~CAS0: CN2.a3
~CAS2: CN2.b23
~CASEL: CN3.b26
~CCAS0: CN3.b16
~CCAS2: CN3.b21
~CCE0: CN3.b17
~CLWR: CN3.b28
~CSYNC: R48.2, R801.1
~DISK: CN2.b2
~DTAK: CN3.b20
~FDC: CN2.a24
~FDWR: CN2.b24
~FRES: CN2.a25
~HSYNC: CN3.b14
~JAP: U1.10 (RC0)
~LWR: CN2.b21
~M3: CN3.b30
~MRES: CE15.1, CN3.b2, D1.2 (BA), R65.2, R66.1
~RAS2: R63.1
~ROM: CN2.a21
~SRES: IC10.1, R67.2
~TIME: CN3.b31
~UWR: CN2.b22, CN3.b29
~VRES: CN3.b27
~VSYNC: CN3.b13
~WRES: R701.1, U1.11 (RA2)
~XAS: CN3.b18
~YS0: CN3.b12

Notes on the sheet:
L507 value 100uH if IC513 is NCP3063/NCV3063
MD VCC is used as +5V on 32X
Install RX500 if IC513 is NCP3063/NCV3063
Integrated switchless region and 50/60Hz mod
32X power
Mega Drive power
Integrated "triple bypass" RGB amp
Pull-ups original to MD, also required for "triple bypass"
