RGBeter/Neptune/sge.kicad_sch

## KiCad design sge.kicad_sch (2025-06-26, an earlier design)

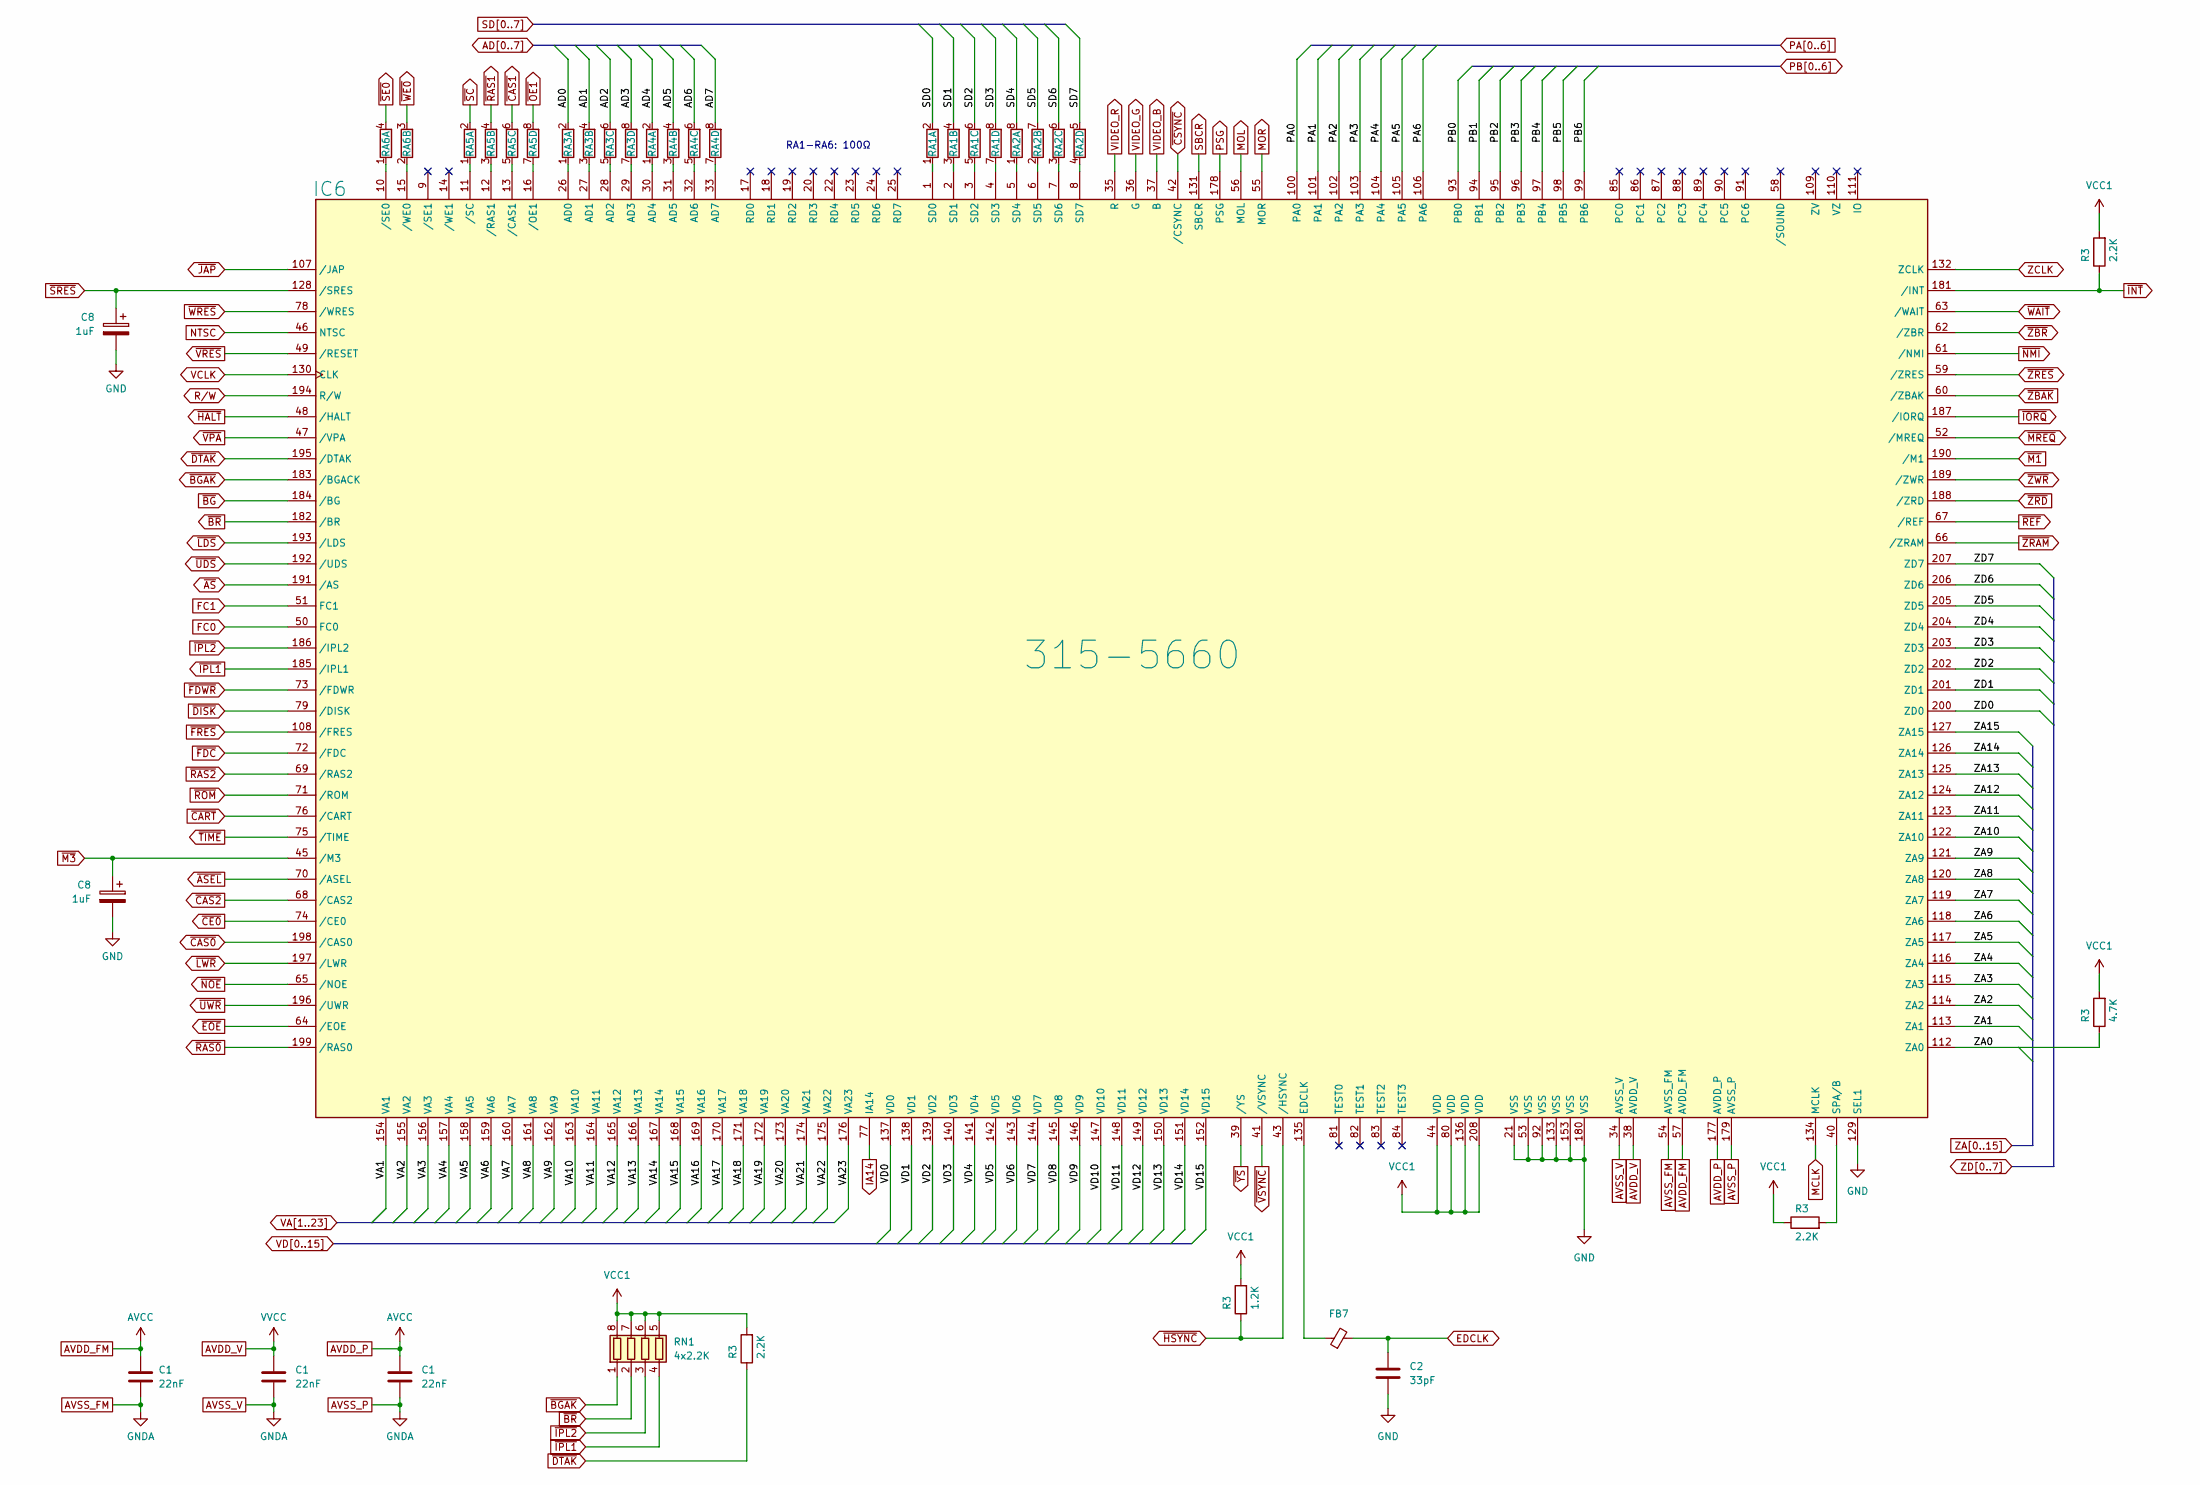
[picture p13: schematic sge.kicad_sch]

Parts:
C1: 22nF
C2: 33pF
C8: 1uF
FB7: (no value)
IC6: 315-5660; LQFP-208_28x28mm_P0.5mm
R3: 2.2K
RA1, RA2, RA3, RA4, RA5: 4x100
RA6: 2x100
RN1: 4x2.2K

Connections:
AD0: RA3.2 (R1.2)
AD1: RA3.4 (R2.2)
AD2: RA3.6 (R3.2)
AD3: RA3.8 (R4.2)
AD4: RA4.2 (R1.2)
AD5: RA4.4 (R2.2)
AD6: RA4.6 (R3.2)
AD7: RA4.8 (R4.2)
AVCC: C1.1, IC6.57 (AVDD_FM), IC6.177 (AVDD_P)
AVDD_V: C1.1, IC6.38 (AVDD_V)
AVSS_FM: C1.2, IC6.34 (AVSS_V), IC6.54 (AVSS_FM), IC6.179 (AVSS_P)
EDCLK: C2.1, FB7.2
FC0: IC6.50 (FC0)
FC1: IC6.51 (FC1)
GND: C2.2, C8.2, IC6.21 (VSS), IC6.53 (VSS), IC6.92 (VSS), IC6.129 (SEL1), IC6.133 (VSS), IC6.153 (VSS), IC6.180 (VSS)
IA14: IC6.77 (IA14)
MCLK: IC6.134 (MCLK)
MOL: IC6.56 (MOL)
MOR: IC6.55 (MOR)
NTSC: IC6.46 (NTSC)
unnamed: FB7.1, IC6.135 (EDCLK)
unnamed: IC6.1 (SD0), RA1.1 (R1.1)
unnamed: IC6.2 (SD1), RA1.3 (R2.1)
unnamed: IC6.3 (SD2), RA1.5 (R3.1)
unnamed: IC6.4 (SD3), RA1.7 (R4.1)
unnamed: IC6.5 (SD4), RA2.1 (R1.1)
unnamed: IC6.6 (SD5), RA2.2 (R2.1)
unnamed: IC6.7 (SD6), RA2.3 (R3.1)
unnamed: IC6.8 (SD7), RA2.4 (R4.1)
unnamed: IC6.10 (/SE0), RA6.1 (R1.1)
unnamed: IC6.11 (/SC), RA5.1 (R1.1)
unnamed: IC6.12 (/RAS1), RA5.3 (R2.1)
unnamed: IC6.13 (/CAS1), RA5.5 (R3.1)
unnamed: IC6.15 (/WE0), RA6.2 (R2.1)
unnamed: IC6.16 (/OE1), RA5.7 (R4.1)
unnamed: IC6.26 (AD0), RA3.1 (R1.1)
unnamed: IC6.27 (AD1), RA3.3 (R2.1)
unnamed: IC6.28 (AD2), RA3.5 (R3.1)
unnamed: IC6.29 (AD3), RA3.7 (R4.1)
unnamed: IC6.30 (AD4), RA4.1 (R1.1)
unnamed: IC6.31 (AD5), RA4.3 (R2.1)
unnamed: IC6.32 (AD6), RA4.5 (R3.1)
unnamed: IC6.33 (AD7), RA4.7 (R4.1)
unnamed: IC6.40 (SPA/B), R3.2
PA0: IC6.100 (PA0)
PA1: IC6.101 (PA1)
PA2: IC6.102 (PA2)
PA3: IC6.103 (PA3)
PA4: IC6.104 (PA4)
PA5: IC6.105 (PA5)
PA6: IC6.106 (PA6)
PB0: IC6.93 (PB0)
PB1: IC6.94 (PB1)
PB2: IC6.95 (PB2)
PB3: IC6.96 (PB3)
PB4: IC6.97 (PB4)
PB5: IC6.98 (PB5)
PB6: IC6.99 (PB6)
PSG: IC6.178 (PSG)
R/W: IC6.194 (R/W)
SBCR: IC6.131 (SBCR)
SD0: RA1.2 (R1.2)
SD1: RA1.4 (R2.2)
SD2: RA1.6 (R3.2)
SD3: RA1.8 (R4.2)
SD4: RA2.8 (R1.2)
SD5: RA2.7 (R2.2)
SD6: RA2.6 (R3.2)
SD7: RA2.5 (R4.2)
VA1: IC6.154 (VA1)
VA2: IC6.155 (VA2)
VA3: IC6.156 (VA3)
VA4: IC6.157 (VA4)
VA5: IC6.158 (VA5)
VA6: IC6.159 (VA6)
VA7: IC6.160 (VA7)
VA8: IC6.161 (VA8)
VA9: IC6.162 (VA9)
VA10: IC6.163 (VA10)
VA11: IC6.164 (VA11)
VA12: IC6.165 (VA12)
VA13: IC6.166 (VA13)
VA14: IC6.167 (VA14)
VA15: IC6.168 (VA15)
VA16: IC6.169 (VA16)
VA17: IC6.170 (VA17)
VA18: IC6.171 (VA18)
VA19: IC6.172 (VA19)
VA20: IC6.173 (VA20)
VA21: IC6.174 (VA21)
VA22: IC6.175 (VA22)
VA23: IC6.176 (VA23)
VCC1: IC6.44 (VDD), IC6.80 (VDD), IC6.136 (VDD), IC6.208 (VDD), R3.1, R3.2, RN1.5 (R4.2), RN1.6 (R3.2), RN1.7 (R2.2), RN1.8 (R1.2)
VCLK: IC6.130 (CLK)
VD0: IC6.137 (VD0)
VD1: IC6.138 (VD1)
VD2: IC6.139 (VD2)
VD3: IC6.140 (VD3)
VD4: IC6.141 (VD4)
VD5: IC6.142 (VD5)
VD6: IC6.143 (VD6)
VD7: IC6.144 (VD7)
VD8: IC6.145 (VD8)
VD9: IC6.146 (VD9)
VD10: IC6.147 (VD10)
VD11: IC6.148 (VD11)
VD12: IC6.149 (VD12)
VD13: IC6.150 (VD13)
VD14: IC6.151 (VD14)
VD15: IC6.152 (VD15)
VIDEO_B: IC6.37 (B)
VIDEO_G: IC6.36 (G)
VIDEO_R: IC6.35 (R)
ZA0: IC6.112 (ZA0), R3.1
ZA1: IC6.113 (ZA1)
ZA2: IC6.114 (ZA2)
ZA3: IC6.115 (ZA3)
ZA4: IC6.116 (ZA4)
ZA5: IC6.117 (ZA5)
ZA6: IC6.118 (ZA6)
ZA7: IC6.119 (ZA7)
ZA8: IC6.120 (ZA8)
ZA9: IC6.121 (ZA9)
ZA10: IC6.122 (ZA10)
ZA11: IC6.123 (ZA11)
ZA12: IC6.124 (ZA12)
ZA13: IC6.125 (ZA13)
ZA14: IC6.126 (ZA14)
ZA15: IC6.127 (ZA15)
ZCLK: IC6.132 (ZCLK)
ZD0: IC6.200 (ZD0)
ZD1: IC6.201 (ZD1)
ZD2: IC6.202 (ZD2)
ZD3: IC6.203 (ZD3)
ZD4: IC6.204 (ZD4)
ZD5: IC6.205 (ZD5)
ZD6: IC6.206 (ZD6)
ZD7: IC6.207 (ZD7)
~ASEL: IC6.70 (/ASEL)
~AS: IC6.191 (/AS)
~BGAK: IC6.183 (/BGACK), RN1.1 (R1.1)
~BG: IC6.184 (/BG)
~BR: IC6.182 (/BR), RN1.2 (R2.1)
~CART: IC6.76 (/CART)
~CAS0: IC6.198 (/CAS0)
~CAS1: RA5.6 (R3.2)
~CAS2: IC6.68 (/CAS2)
~CE0: IC6.74 (/CE0)
~CSYNC: IC6.42 (/CSYNC)
~DISK: IC6.79 (/DISK)
~DTAK: IC6.195 (/DTAK), R3.1
~EOE: IC6.64 (/EOE)
~FDC: IC6.72 (/FDC)
~FDWR: IC6.73 (/FDWR)
~FRES: IC6.108 (/FRES)
~HALT: IC6.48 (/HALT)
~HSYNC: IC6.43 (/HSYNC), R3.1
~INT: IC6.181 (/INT), R3.1
~IORQ: IC6.187 (/IORQ)
~IPL1: IC6.185 (/IPL1), RN1.4 (R4.1)
~IPL2: IC6.186 (/IPL2), RN1.3 (R3.1)
~JAP: IC6.107 (/JAP)
~LDS: IC6.193 (/LDS)
~LWR: IC6.197 (/LWR)
~M1: IC6.190 (/M1)
~M3: C8.1, IC6.45 (/M3)
~MREQ: IC6.52 (/MREQ)
~NMI: IC6.61 (/NMI)
~NOE: IC6.65 (/NOE)
~OE1: RA5.8 (R4.2)
~RAS0: IC6.199 (/RAS0)
~RAS1: RA5.4 (R2.2)
~RAS2: IC6.69 (/RAS2)
~REF: IC6.67 (/REF)
~ROM: IC6.71 (/ROM)
~SC: RA5.2 (R1.2)
~SE0: RA6.4 (R1.2)
~SRES: C8.1, IC6.128 (/SRES)
~TIME: IC6.75 (/TIME)
~UDS: IC6.192 (/UDS)
~UWR: IC6.196 (/UWR)
~VPA: IC6.47 (/VPA)
~VRES: IC6.49 (/RESET)
~VSYNC: IC6.41 (/VSYNC)
~WAIT: IC6.63 (/WAIT)
~WE0: RA6.3 (R2.2)
~WRES: IC6.78 (/WRES)
~YS: IC6.39 (/YS)
~ZBAK: IC6.60 (/ZBAK)
~ZBR: IC6.62 (/ZBR)
~ZRAM: IC6.66 (/ZRAM)
~ZRD: IC6.188 (/ZRD)
~ZRES: IC6.59 (/ZRES)
~ZWR: IC6.189 (/ZWR)

Notes on the sheet:
RA1-RA6: 100Ω
