RGBeter/Neptune/z80.kicad_sch

## KiCad design z80.kicad_sch (2025-06-26, an earlier design)

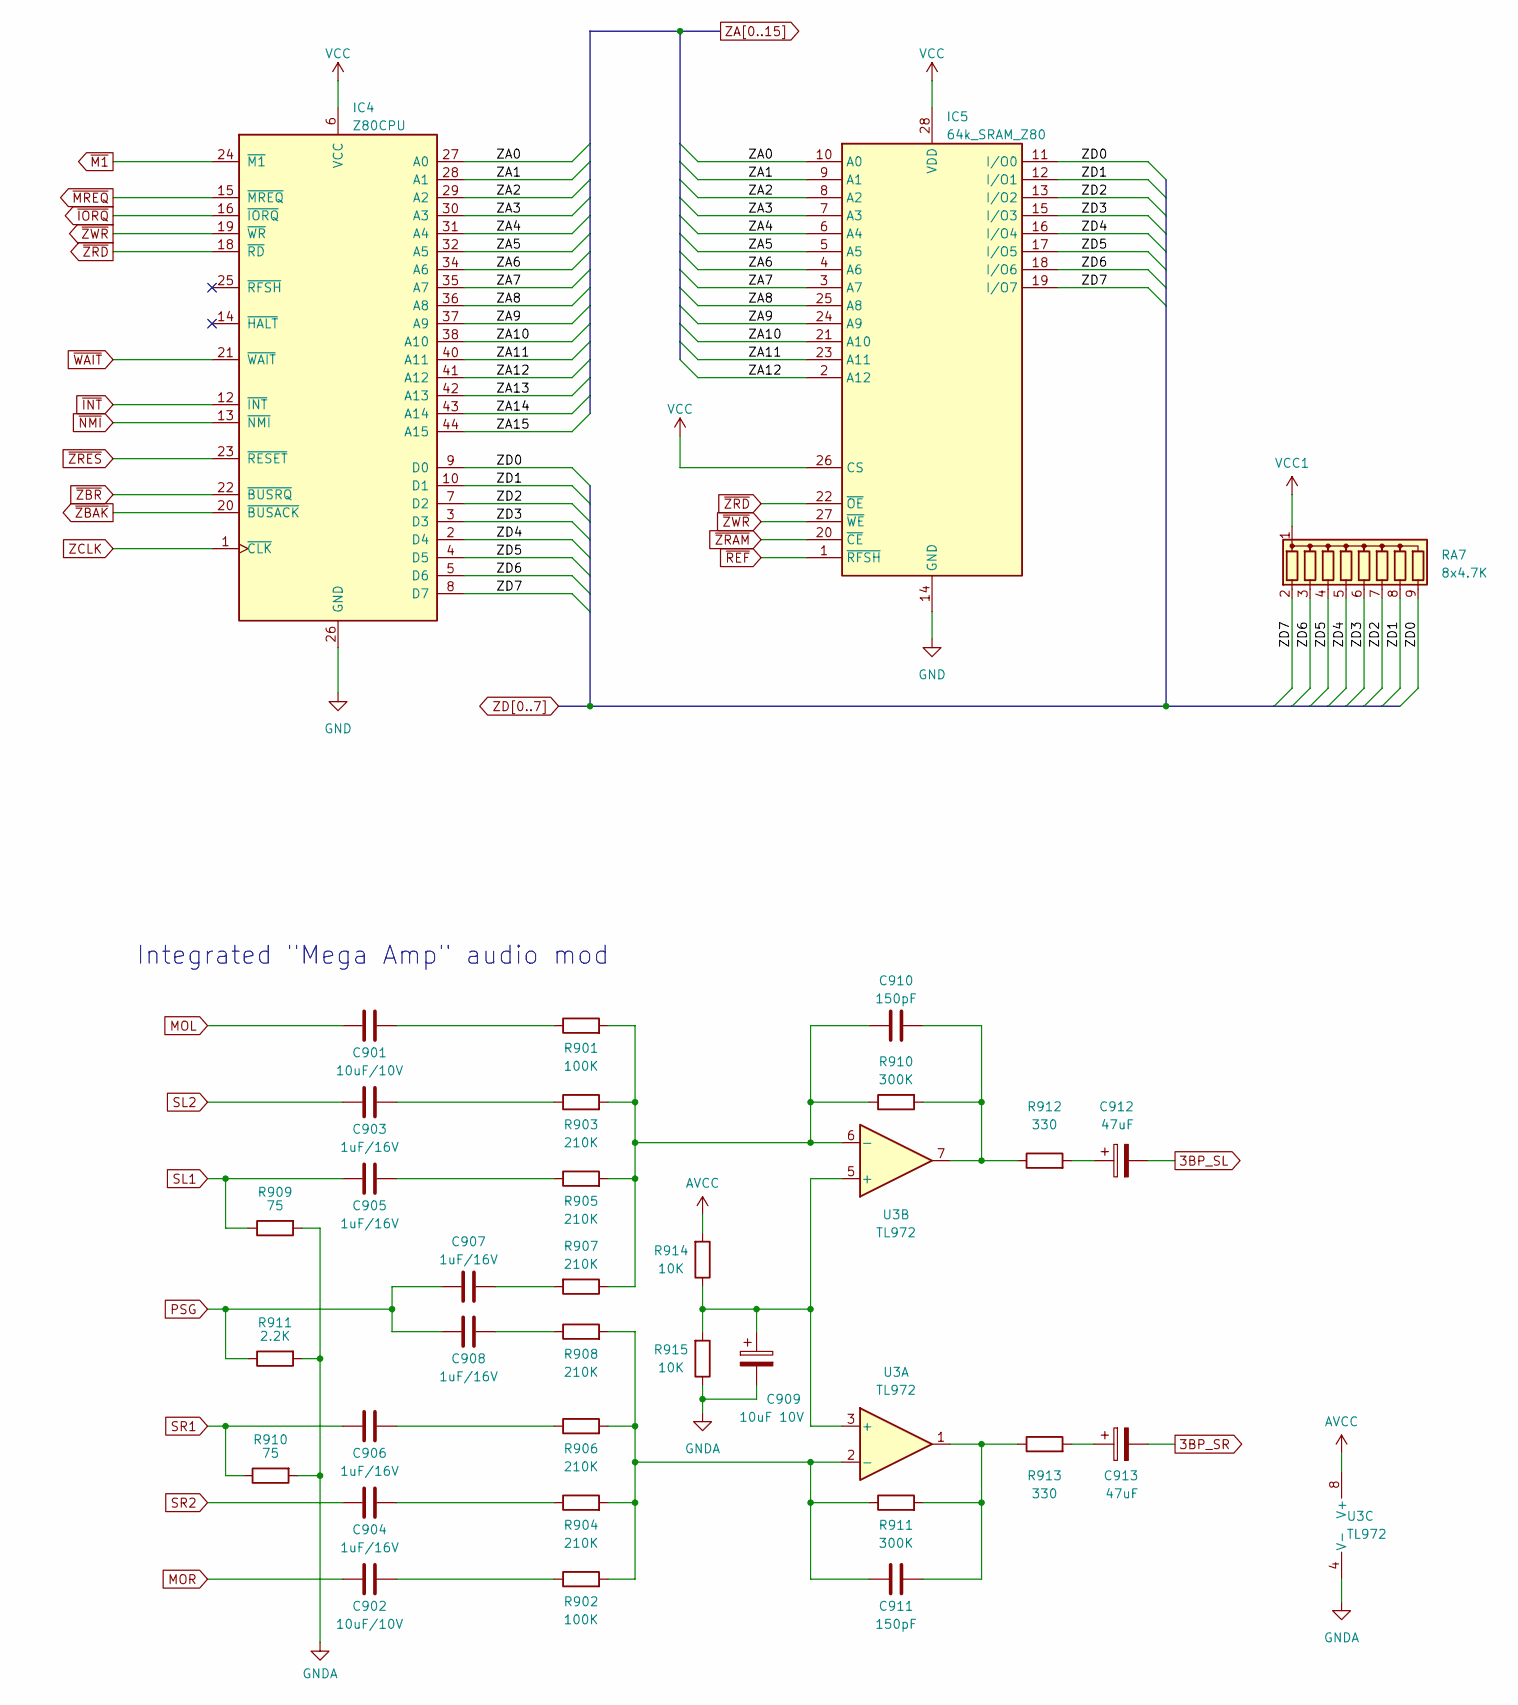
[picture p14: schematic z80.kicad_sch]

Parts:
C901, C902: 10uF/10V
C903, C904, C905, C906, C907, C908: 1uF/16V
C909: 10uF 10V
C910, C911: 150pF
C912, C913: 47uF
IC4: Z80CPU; LQFP-44_10x10mm_P0.8mm
IC5: 64k_SRAM_Z80; SSOP-28_3.9x9.9mm_P0.635mm
R901, R902: 100K
R903, R904, R905, R906, R907, R908: 210K
R909, R910: 75
R911: 2.2K
R912, R913: 330
R914, R915: 10K
RA7: 8x4.7K
U3: TL972

Connections:
3BP_SL: C912.2
3BP_SR: C913.2
AVCC: R914.2, U3.8 (V+)
GND: IC4.26 (GND), IC5.14 (GND)
GNDA: C909.2, R909.2, R910.2, R911.2, R915.1, U3.4 (V-)
MOL: C901.1
MOR: C902.1
unnamed: C901.2, R901.1
unnamed: C902.2, R902.1
unnamed: C903.2, R903.1
unnamed: C904.2, R904.1
unnamed: C905.2, R905.1
unnamed: C906.2, R906.1
unnamed: C907.2, R907.2
unnamed: C908.2, R908.1
unnamed: C909.1, R914.1, R915.2, U3.3 (+), U3.5 (+)
unnamed: C910.1, R901.2, R903.2, R905.2, R907.1, R910.1, U3.6 (-)
unnamed: C910.2, R910.2, R912.1, U3.7
unnamed: C911.1, R902.2, R904.2, R906.2, R908.2, R911.1, U3.2 (-)
unnamed: C911.2, R911.2, R913.1, U3.1
unnamed: C912.1, R912.2
unnamed: C913.1, R913.2
PSG: C907.1, C908.1, R911.1
SL1: C905.1, R909.1
SL2: C903.1
SR1: C906.1, R910.1
SR2: C904.1
VCC: IC4.6 (VCC), IC5.26 (CS), IC5.28 (VDD)
VCC1: RA7.1 (common)
ZA0: IC4.27 (A0), IC5.10 (A0)
ZA1: IC4.28 (A1), IC5.9 (A1)
ZA2: IC4.29 (A2), IC5.8 (A2)
ZA3: IC4.30 (A3), IC5.7 (A3)
ZA4: IC4.31 (A4), IC5.6 (A4)
ZA5: IC4.32 (A5), IC5.5 (A5)
ZA6: IC4.34 (A6), IC5.4 (A6)
ZA7: IC4.35 (A7), IC5.3 (A7)
ZA8: IC4.36 (A8), IC5.25 (A8)
ZA9: IC4.37 (A9), IC5.24 (A9)
ZA10: IC4.38 (A10), IC5.21 (A10)
ZA11: IC4.40 (A11), IC5.23 (A11)
ZA12: IC4.41 (A12), IC5.2 (A12)
ZA13: IC4.42 (A13)
ZA14: IC4.43 (A14)
ZA15: IC4.44 (A15)
ZCLK: IC4.1 (~CLK)
ZD0: IC4.9 (D0), IC5.11 (I/O0), RA7.9 (R8)
ZD1: IC4.10 (D1), IC5.12 (I/O1), RA7.8 (R7)
ZD2: IC4.7 (D2), IC5.13 (I/O2), RA7.7 (R6)
ZD3: IC4.3 (D3), IC5.15 (I/O3), RA7.6 (R5)
ZD4: IC4.2 (D4), IC5.16 (I/O4), RA7.5 (R4)
ZD5: IC4.4 (D5), IC5.17 (I/O5), RA7.4 (R3)
ZD6: IC4.5 (D6), IC5.18 (I/O6), RA7.3 (R2)
ZD7: IC4.8 (D7), IC5.19 (I/O7), RA7.2 (R1)
~INT: IC4.12 (~INT)
~IORQ: IC4.16 (~IORQ)
~M1: IC4.24 (~M1)
~MREQ: IC4.15 (~MREQ)
~NMI: IC4.13 (~NMI)
~REF: IC5.1 (~RFSH)
~WAIT: IC4.21 (~WAIT)
~ZBAK: IC4.20 (~BUSACK)
~ZBR: IC4.22 (~BUSRQ)
~ZRAM: IC5.20 (~CE)
~ZRD: IC4.18 (~RD), IC5.22 (~OE)
~ZRES: IC4.23 (~RESET)
~ZWR: IC4.19 (~WR), IC5.27 (~WE)

Notes on the sheet:
Integrated "Mega Amp" audio mod
